zloymalefic/bc250-case/references/printables-1793043-nexgen-pro-v2/AIO Mount/clamping-plate-v2.3mf

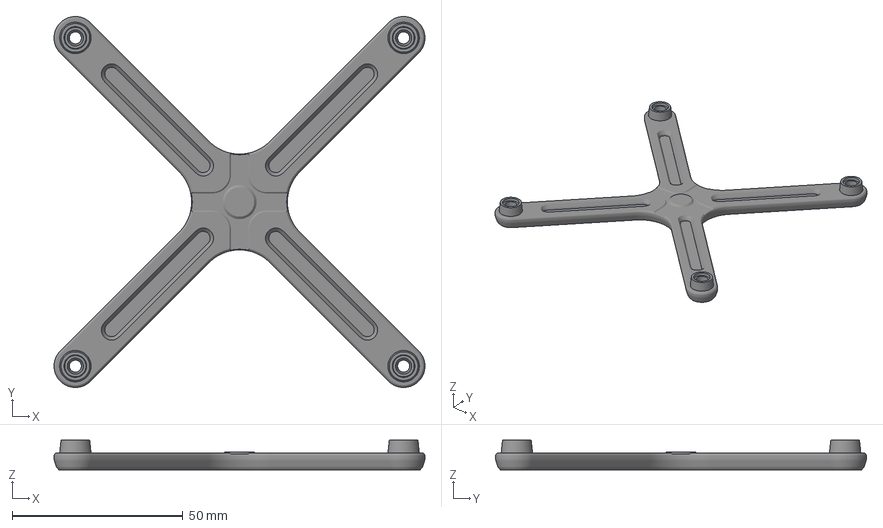
[picture p15: CAD file, 2026-08-19]
references/printables-1793043-nexgen-pro-v2/AIO Mount/clamping-plate-v2.3mf
108.5 x 108.5 x 8.70 mm
