zloymalefic/bc250-case/references/printables-1793043-nexgen-pro-v2/ARGB LED Strip/pro-v2-argb-strip-mount.3mf

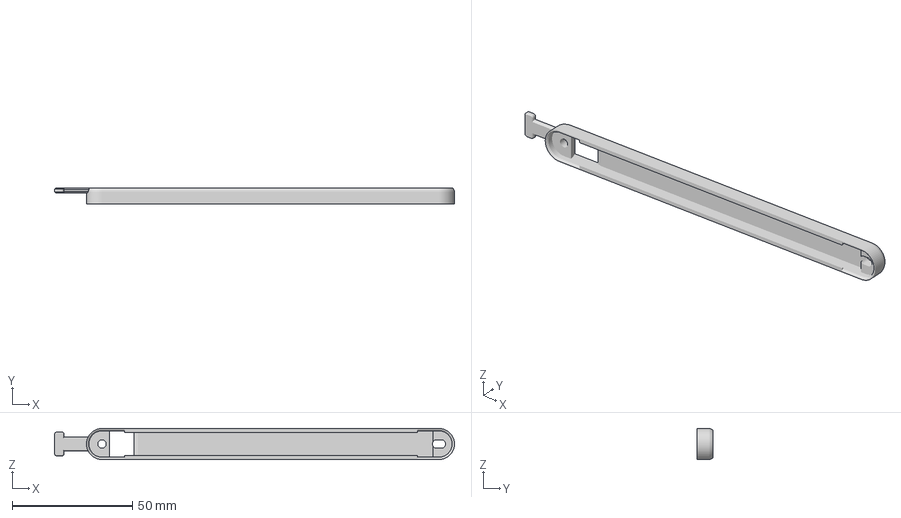
[picture p16: CAD file, 2026-08-19]
references/printables-1793043-nexgen-pro-v2/ARGB LED Strip/pro-v2-argb-strip-mount.3mf
166.2 x 6.60 x 12.9 mm
