zloymalefic/bc250-case/references/printables-1793043-nexgen-pro-v2/Case/pro-v2-rear-case-multi-material.3mf

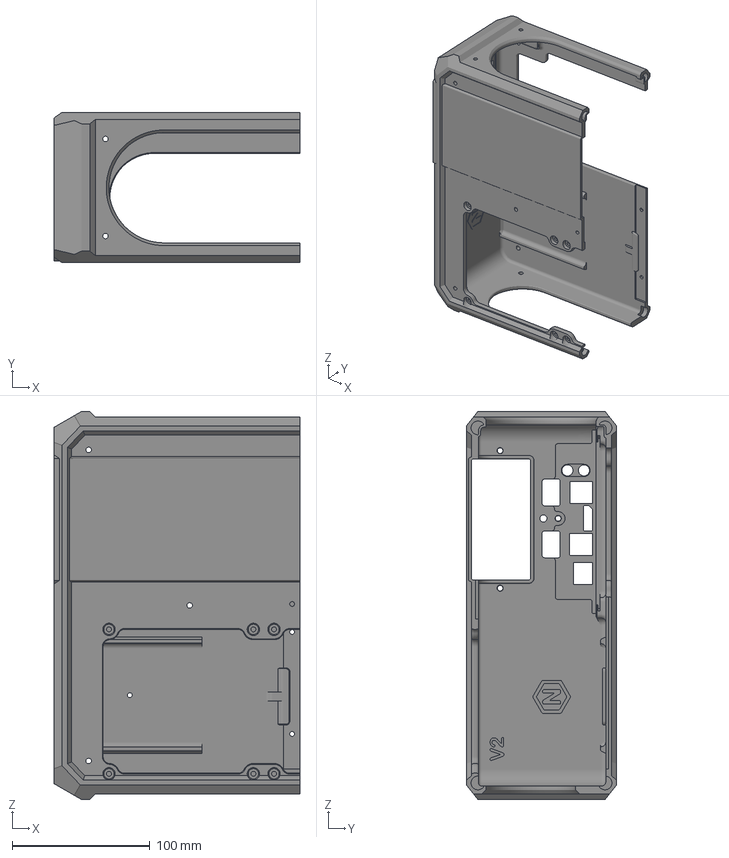
[picture p17: CAD file, 2026-08-19]
references/printables-1793043-nexgen-pro-v2/Case/pro-v2-rear-case-multi-material.3mf
178.6 x 109.4 x 282.1 mm
Case
IO (1)
IO (10)
IO (2)
IO (3)
IO (5)
IO (7)
IO (8)
IO (9)
Lan (1)
Lan (2)
Lan
NXG-Logo-1
NXG-Logo-2
Network Logo
PWR (1)
PWR (2)
PWR
PWR-Loop
RST (1)
RST (2)
RST
RST-Loop
