zloymalefic/bc250-case/references/printables-1793043-nexgen-pro-v2/Foot/pro-long-foot-tpu.3mf

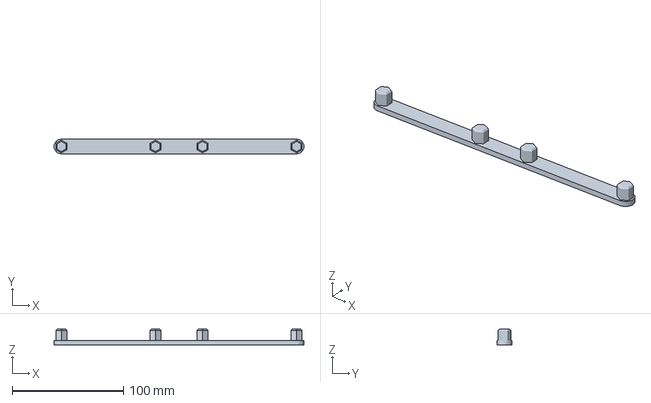
[picture p18: CAD file, 2026-08-19]
references/printables-1793043-nexgen-pro-v2/Foot/pro-long-foot-tpu.3mf
225.2 x 13.2 x 14.0 mm
