zloymalefic/bc250-case/references/printables-1793043-nexgen-pro-v2/Latest Face Plate Design - (Version 2.1)/blank-face-plate.step

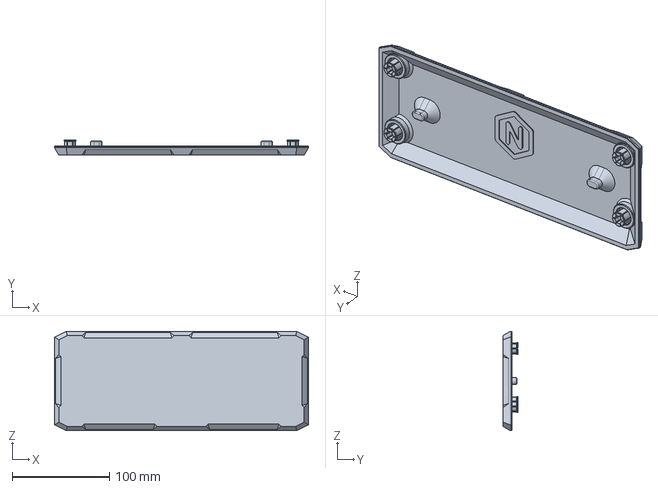
[picture p19: CAD file, 2026-08-19]
references/printables-1793043-nexgen-pro-v2/Latest Face Plate Design - (Version 2.1)/blank-face-plate.step
260.9 x 15.7 x 102.0 mm
