zloymalefic/bc250-case/references/printables-1793043-nexgen-pro-v2/Left Hand Hex Panel/pro-v2-lh-hex-panel-no-logo-edition.3mf

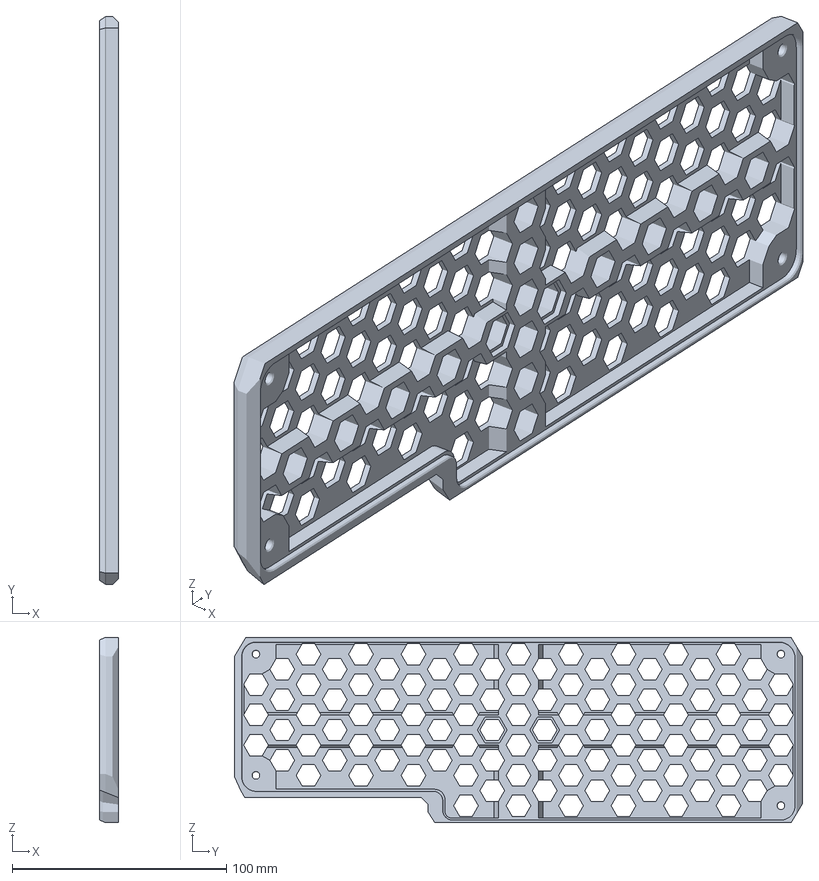
[picture p20: CAD file, 2026-08-19]
references/printables-1793043-nexgen-pro-v2/Left Hand Hex Panel/pro-v2-lh-hex-panel-no-logo-edition.3mf
9.00 x 264.9 x 86.4 mm
