zloymalefic/bc250-case/references/printables-1793043-nexgen-pro-v2/Power Button/pro-v2-button-mounting-plate.3mf

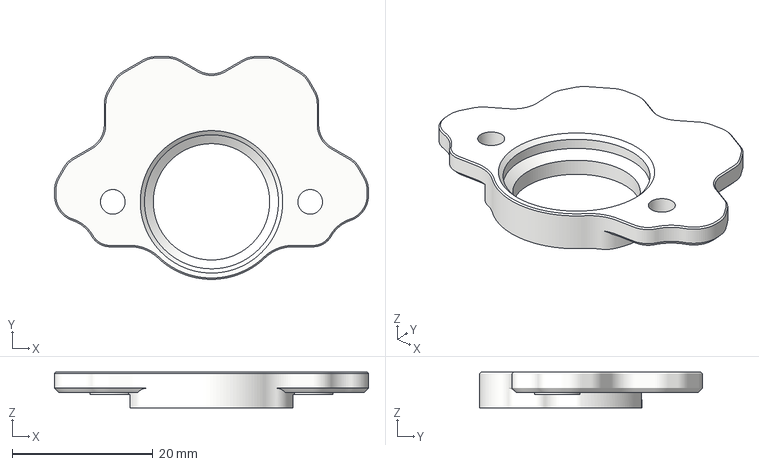
[picture p21: CAD file, 2026-08-19]
references/printables-1793043-nexgen-pro-v2/Power Button/pro-v2-button-mounting-plate.3mf
44.5 x 31.6 x 5.10 mm
