zloymalefic/bc250-case/references/printables-1793043-nexgen-pro-v2/Power Supply Mounts/pro-v2-meanwell-lop-mount-400-500-600.3mf

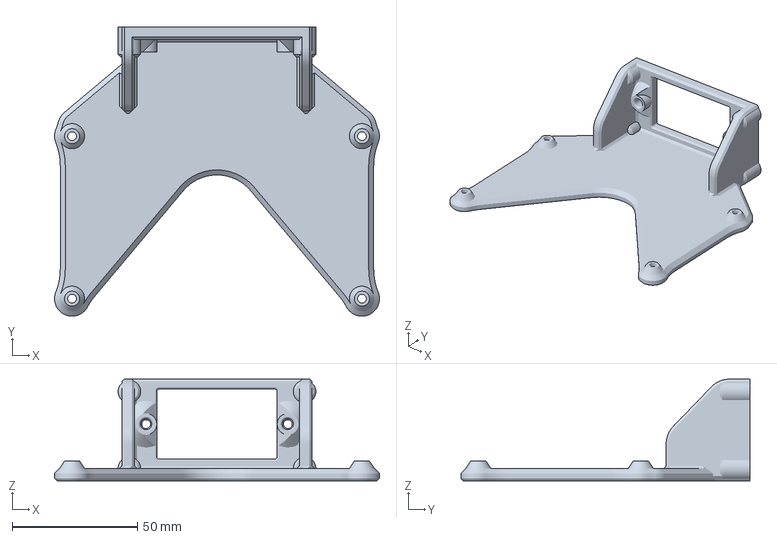
[picture p22: CAD file, 2026-08-19]
references/printables-1793043-nexgen-pro-v2/Power Supply Mounts/pro-v2-meanwell-lop-mount-400-500-600.3mf
129.6 x 115.4 x 40.6 mm
