zloymalefic/bc250-case/references/printables-1793043-nexgen-pro-v2/Right Hand Hex Panel/pro-v2-rh-hex-panel-rune-stone-edition.3mf

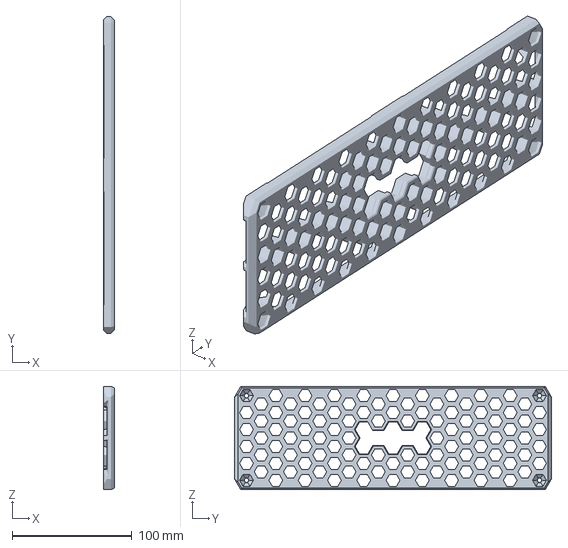
[picture p23: CAD file, 2026-08-19]
references/printables-1793043-nexgen-pro-v2/Right Hand Hex Panel/pro-v2-rh-hex-panel-rune-stone-edition.3mf
9.00 x 264.9 x 86.4 mm
