zloymalefic/bc250-case/references/printables-1793043-nexgen-pro-v2/Top and Bottom Hex Panels/pro-v2-top-hex-panel.3mf

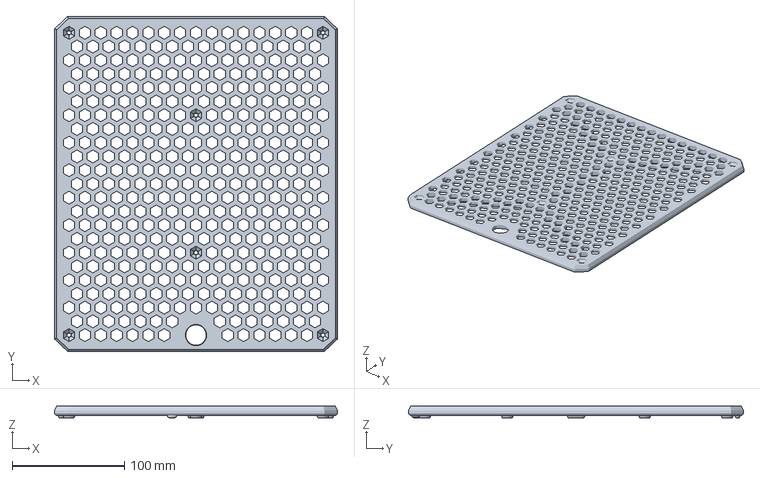
[picture p24: CAD file, 2026-08-19]
references/printables-1793043-nexgen-pro-v2/Top and Bottom Hex Panels/pro-v2-top-hex-panel.3mf
252.1 x 298.5 x 10.9 mm
