zloymalefic/bc250-case/references/printables-1793043-nexgen-pro-v2/Vertical Stand/vertical-stand-optio-1-tpu.3mf

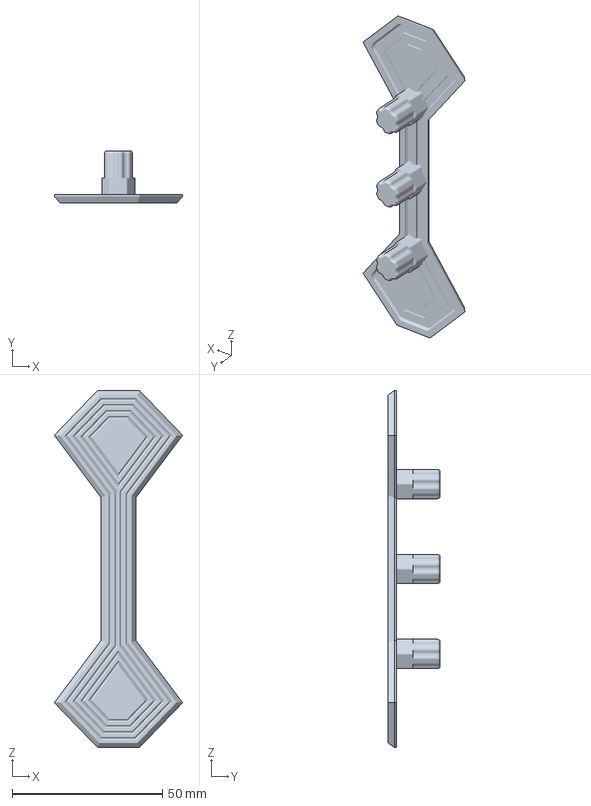
[picture p25: CAD file, 2026-08-19]
references/printables-1793043-nexgen-pro-v2/Vertical Stand/vertical-stand-optio-1-tpu.3mf
42.7 x 17.4 x 118.8 mm
