zloymalefic/bc250-case/visualization/assets/esp32-cover.stl

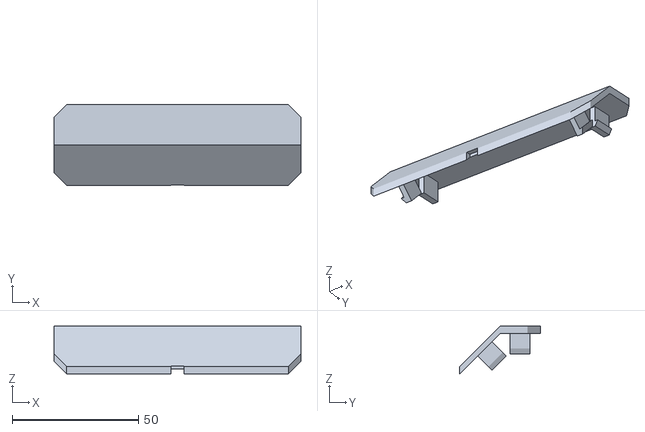
[picture p26: CAD file, 2026-08-20]
visualization/assets/esp32-cover.stl
98.0 x 32.0 x 19.0
