zloymalefic/bc250-case/references/printables-1649679-nexgen-redux/Case V4.2 - Current Version/redux-front-case-42.3mf

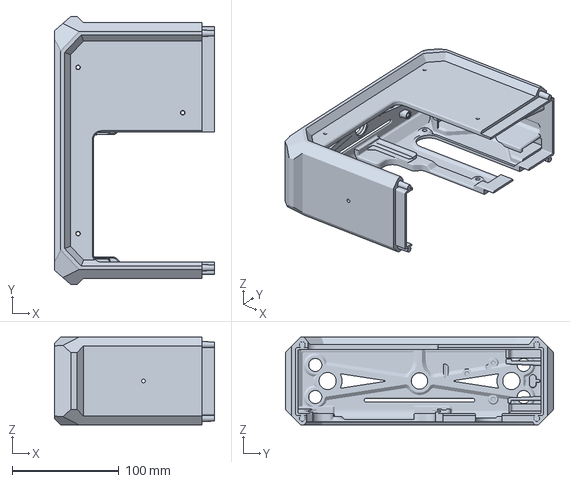
[picture p27: CAD file, 2026-08-20]
references/printables-1649679-nexgen-redux/Case V4.2 - Current Version/redux-front-case-42.3mf
149.7 x 251.1 x 82.3 mm
