zloymalefic/bc250-case/references/printables-1649679-nexgen-redux/Face Plates V4.2/blank-faceplate.step

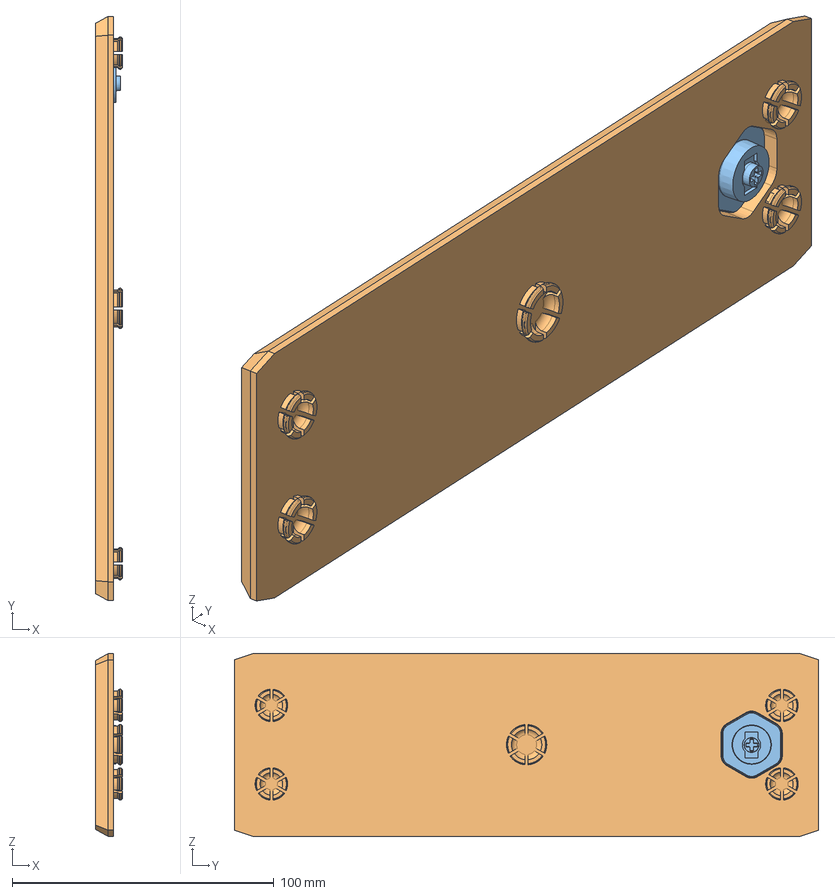
[picture p29: CAD file, 2026-08-20]
references/printables-1649679-nexgen-redux/Face Plates V4.2/blank-faceplate.step
10.2 x 223.2 x 69.9 mm
Blank Button for Generic Latching Switch
Blank REDUX Faceplate
Blank Button for FSP500 PCB
Blank Button to Convert Switch to Momentary
