zloymalefic/bc250-case/references/printables-1649679-nexgen-redux/Fan Mount and Feet V4.2 - Current Version/optional-long-foot-tpu.3mf

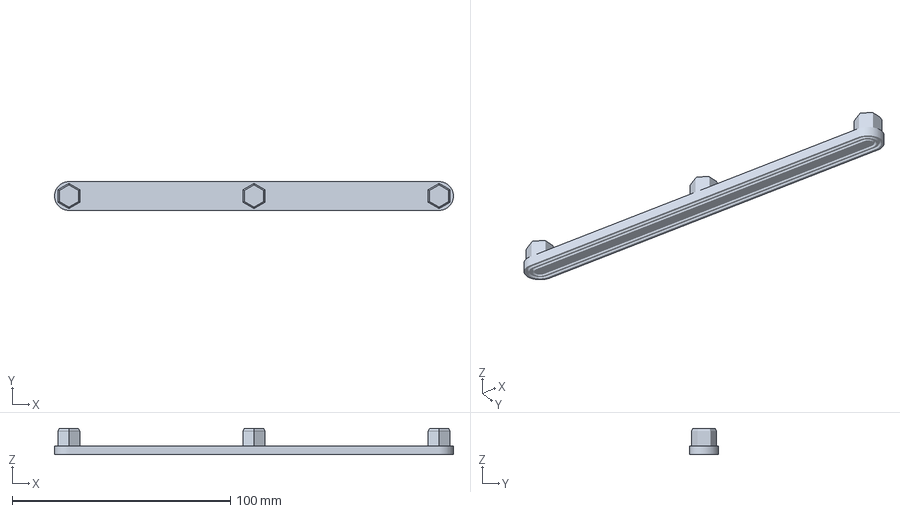
[picture p30: CAD file, 2026-08-20]
references/printables-1649679-nexgen-redux/Fan Mount and Feet V4.2 - Current Version/optional-long-foot-tpu.3mf
182.8 x 13.2 x 12.0 mm
