zloymalefic/bc250-case/references/printables-1649679-nexgen-redux/Optional Parts - Current Version/redux-clamping-plate-v43.3mf

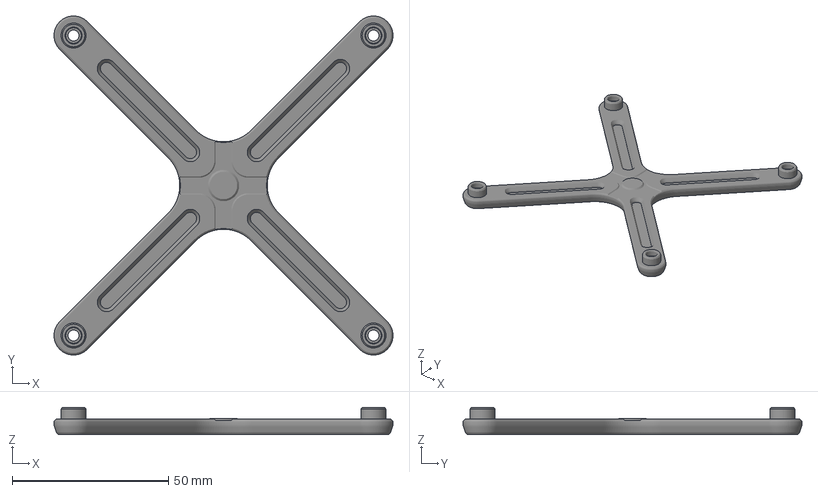
[picture p32: CAD file, 2026-08-20]
references/printables-1649679-nexgen-redux/Optional Parts - Current Version/redux-clamping-plate-v43.3mf
108.5 x 108.5 x 8.80 mm
