zloymalefic/bc250-case/references/printables-1649679-nexgen-redux/Split Hex Covers for 220x220mm or Larger/top-split-panel-a.3mf

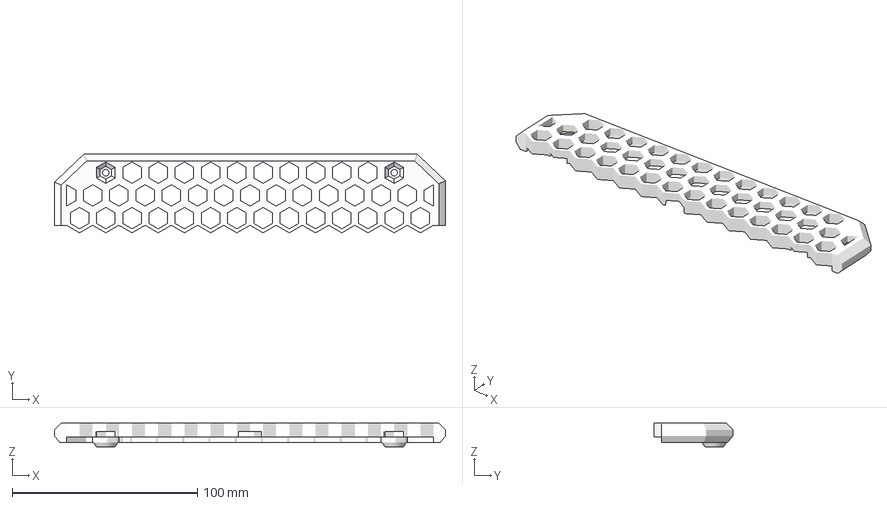
[picture p33: CAD file, 2026-08-20]
references/printables-1649679-nexgen-redux/Split Hex Covers for 220x220mm or Larger/top-split-panel-a.3mf
210.8 x 42.4 x 12.9 mm
