zloymalefic/bc250-case/references/printables-1649679-nexgen-redux/Split Hex Covers for Odd Ball Prusa Beds (250x210)/prusa-priners-only-joiner.3mf

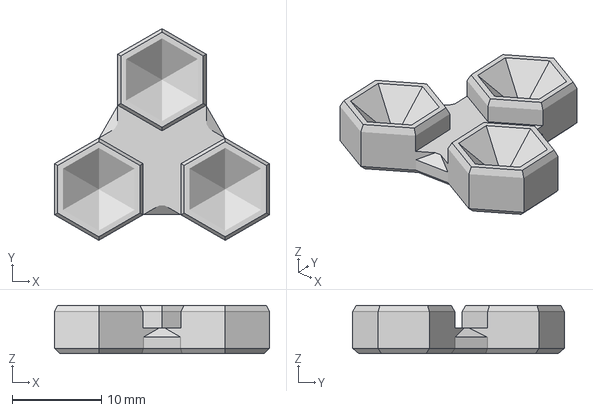
[picture p34: CAD file, 2026-08-20]
references/printables-1649679-nexgen-redux/Split Hex Covers for Odd Ball Prusa Beds (250x210)/prusa-priners-only-joiner.3mf
24.0 x 23.7 x 5.40 mm
