zloymalefic/bc250-case/references/printables-1652979-quiet-case/Deepcool Edition - Digital Display/back-case.stl

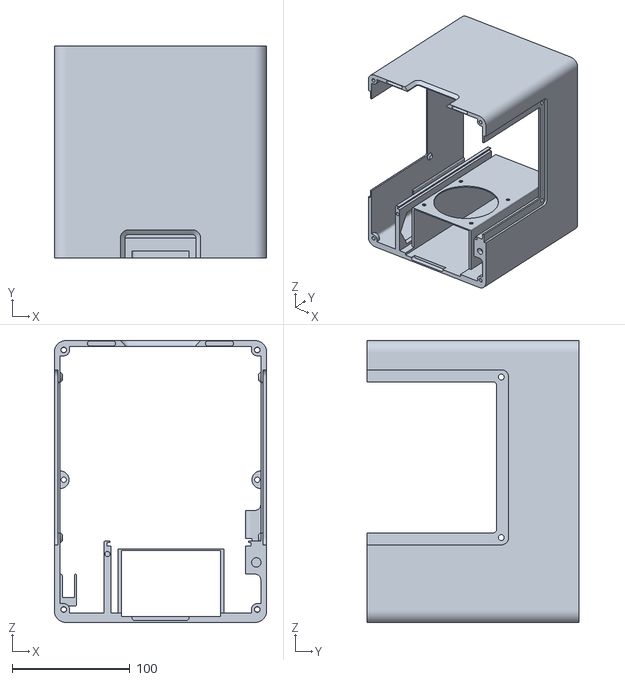
[picture p35: CAD file, 2026-08-19]
references/printables-1652979-quiet-case/Deepcool Edition - Digital Display/back-case.stl
180.0 x 180.0 x 239.0
