zloymalefic/bc250-case/references/printables-1652979-quiet-case/XL Version - Aftermath/panel-front.stl

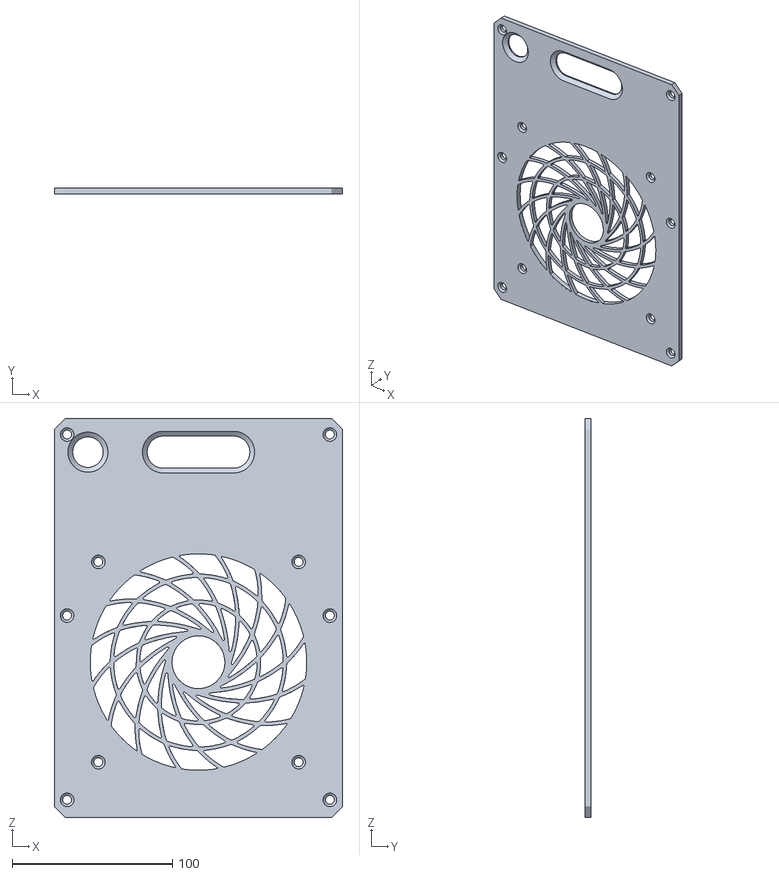
[picture p36: CAD file, 2026-08-19]
references/printables-1652979-quiet-case/XL Version - Aftermath/panel-front.stl
180.0 x 4.01 x 249.0
