zloymalefic/bc250-case/references/printables-1793043-nexgen-pro-v2/AIO Mount/thermalright-mount-bottom-v2.3mf

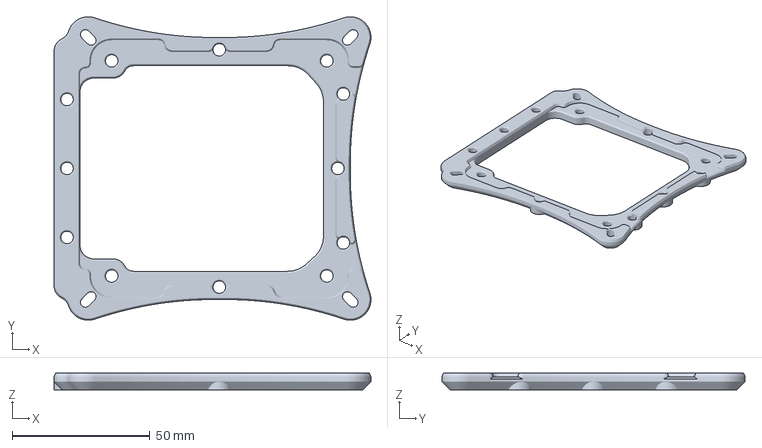
[picture p38: CAD file, 2026-08-19]
references/printables-1793043-nexgen-pro-v2/AIO Mount/thermalright-mount-bottom-v2.3mf
114.9 x 110.0 x 6.10 mm
