zloymalefic/bc250-case/references/printables-1793043-nexgen-pro-v2/ARGB LED Strip/pro-v2-diffuser.3mf

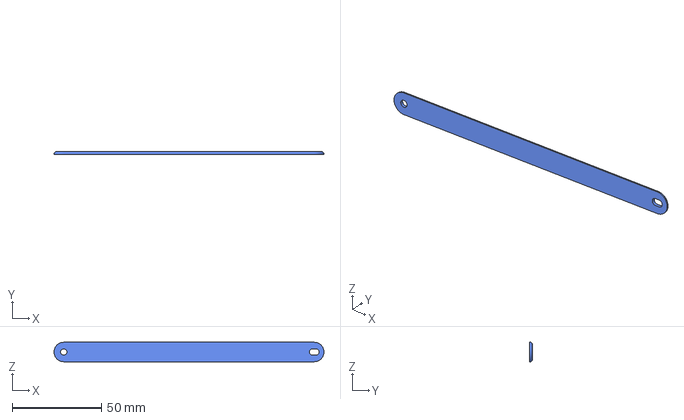
[picture p39: CAD file, 2026-08-19]
references/printables-1793043-nexgen-pro-v2/ARGB LED Strip/pro-v2-diffuser.3mf
150.9 x 1.40 x 10.9 mm
