zloymalefic/bc250-case/references/printables-1793043-nexgen-pro-v2/Case/pro-v2-front-case.3mf

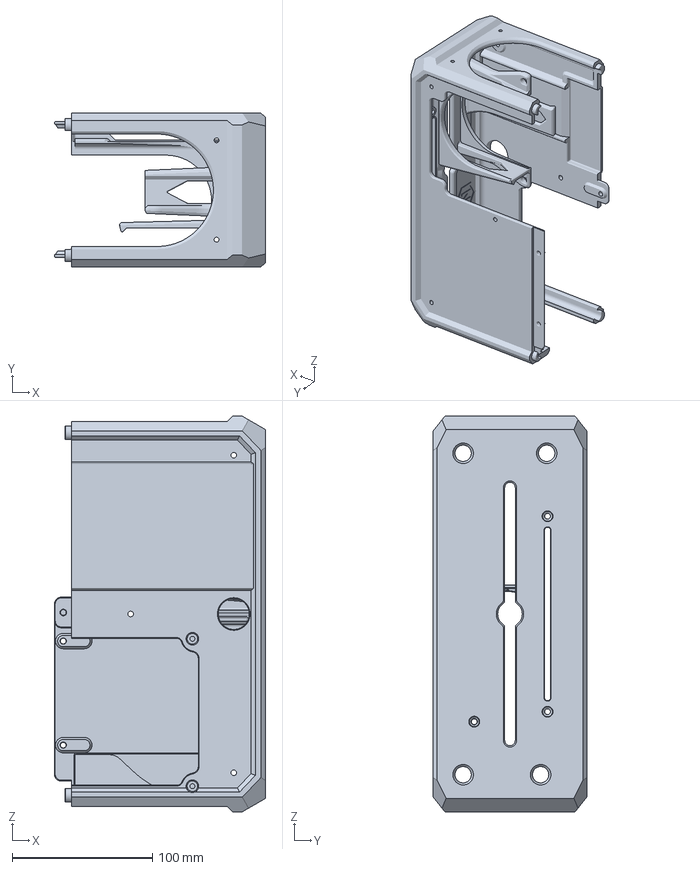
[picture p40: CAD file, 2026-08-19]
references/printables-1793043-nexgen-pro-v2/Case/pro-v2-front-case.3mf
150.5 x 109.4 x 282.0 mm
