zloymalefic/bc250-case/references/printables-1793043-nexgen-pro-v2/Foot/pro-long-foot-petg.3mf

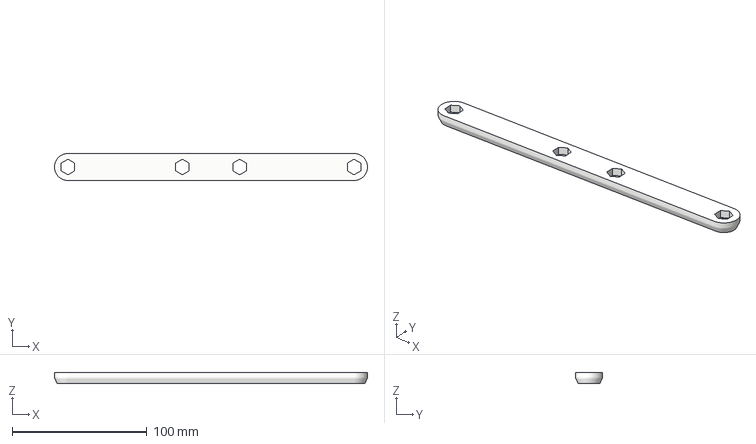
[picture p41: CAD file, 2026-08-19]
references/printables-1793043-nexgen-pro-v2/Foot/pro-long-foot-petg.3mf
232.0 x 20.0 x 8.00 mm
