zloymalefic/bc250-case/references/printables-1793043-nexgen-pro-v2/Latest Face Plate Design - (Version 2.1)/faceplate-option-1.3mf

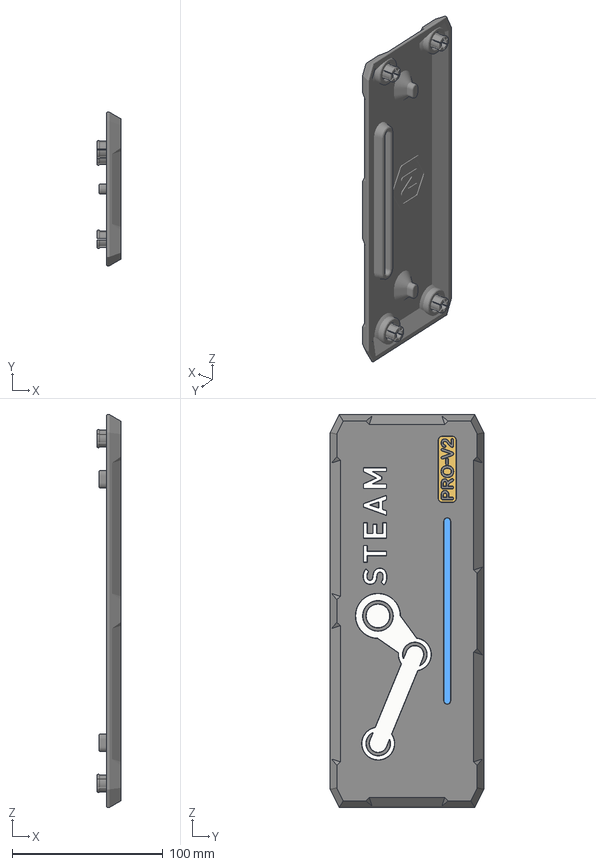
[picture p42: CAD file, 2026-08-19]
references/printables-1793043-nexgen-pro-v2/Latest Face Plate Design - (Version 2.1)/faceplate-option-1.3mf
15.7 x 102.0 x 260.9 mm
Faceplate
LED Strip
Pro Label (1)
Pro Label (2)
Pro Label (3)
Pro Label
Steam Logo (1)
Steam Logo (2)
Steam Logo (3)
Steam Logo (4)
Steam Logo (5)
Steam Logo (6)
Steam Logo
