zloymalefic/bc250-case/references/printables-1793043-nexgen-pro-v2/Left Hand Hex Panel/pro-v2-lh-hex-panel-logo-edition.3mf

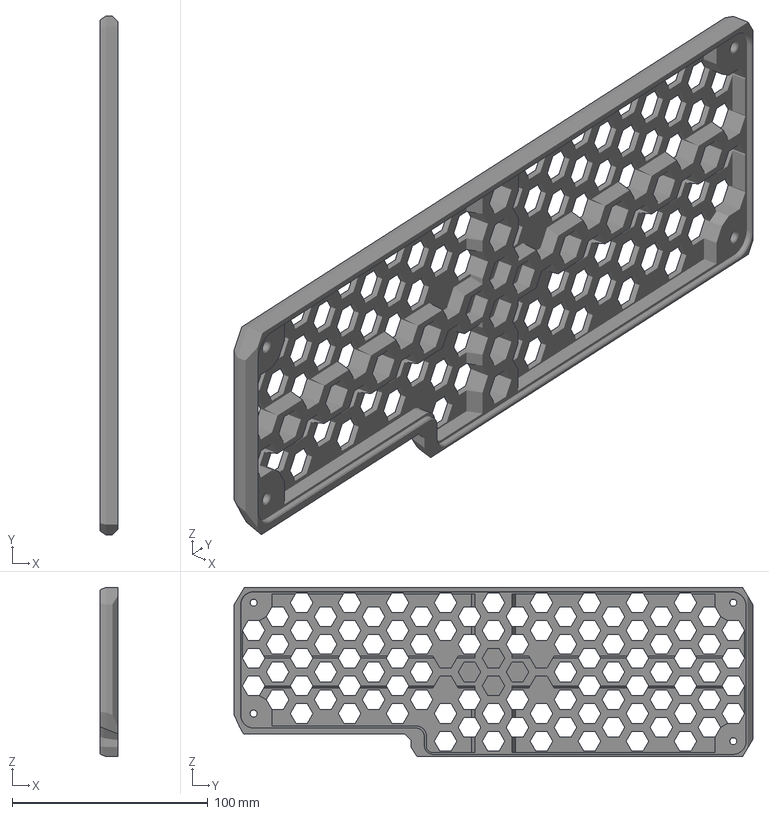
[picture p43: CAD file, 2026-08-19]
references/printables-1793043-nexgen-pro-v2/Left Hand Hex Panel/pro-v2-lh-hex-panel-logo-edition.3mf
9.00 x 264.9 x 86.4 mm
BC-250-Logo (1)
BC-250-Logo (2)
BC-250-Logo (3)
BC-250-Logo
LH Hex Panel (1)
