zloymalefic/bc250-case/references/printables-1793043-nexgen-pro-v2/Power Button/pro-v2-transparent-rear-section.3mf

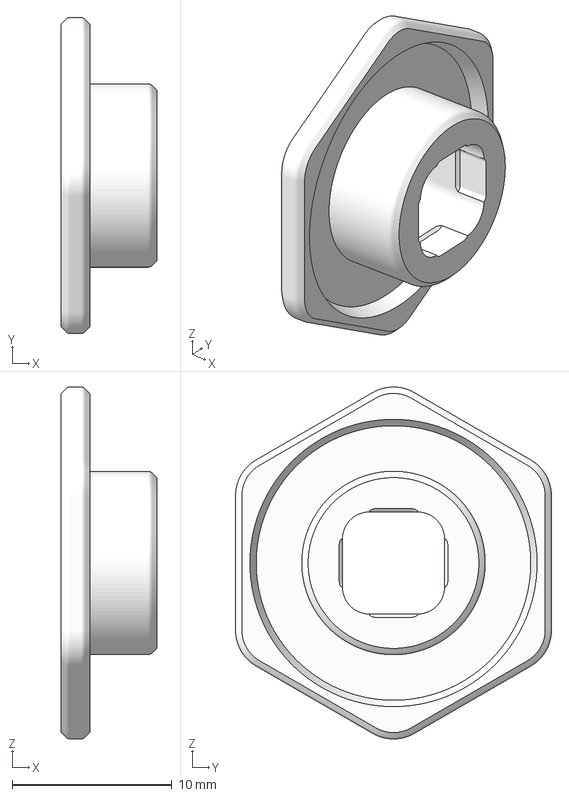
[picture p44: CAD file, 2026-08-19]
references/printables-1793043-nexgen-pro-v2/Power Button/pro-v2-transparent-rear-section.3mf
6.00 x 19.8 x 22.1 mm
