zloymalefic/bc250-case/references/printables-1793043-nexgen-pro-v2/Power Supply Mounts/pro-v2-meanwell-lop-backplate-400-500-600.3mf

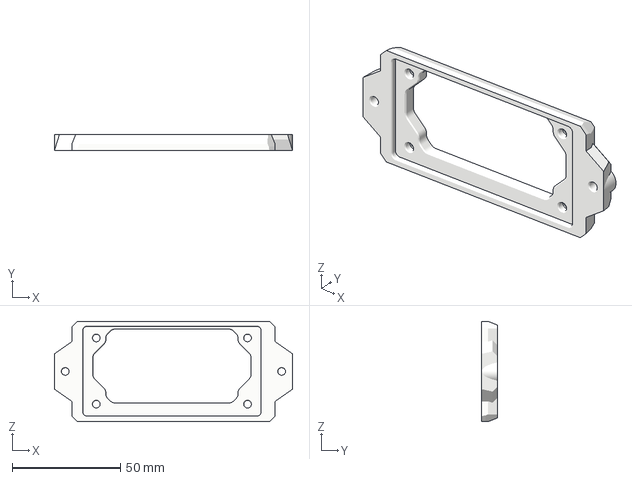
[picture p45: CAD file, 2026-08-19]
references/printables-1793043-nexgen-pro-v2/Power Supply Mounts/pro-v2-meanwell-lop-backplate-400-500-600.3mf
110.0 x 7.20 x 46.3 mm
