zloymalefic/bc250-case/references/printables-1793043-nexgen-pro-v2/Right Hand Hex Panel/rune-stone-argb.3mf

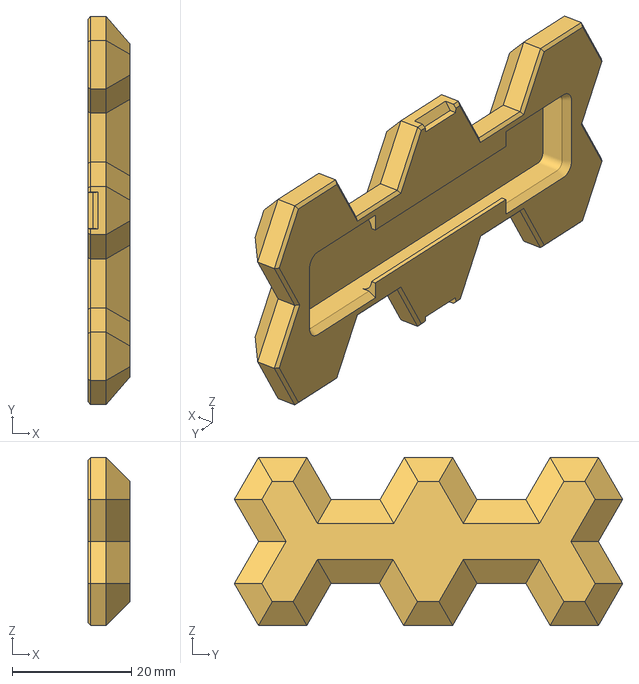
[picture p46: CAD file, 2026-08-19]
references/printables-1793043-nexgen-pro-v2/Right Hand Hex Panel/rune-stone-argb.3mf
7.00 x 65.2 x 28.2 mm
