zloymalefic/bc250-case/references/printables-1793043-nexgen-pro-v2/Vertical Stand/vertical-stand-optio-1-petg.3mf

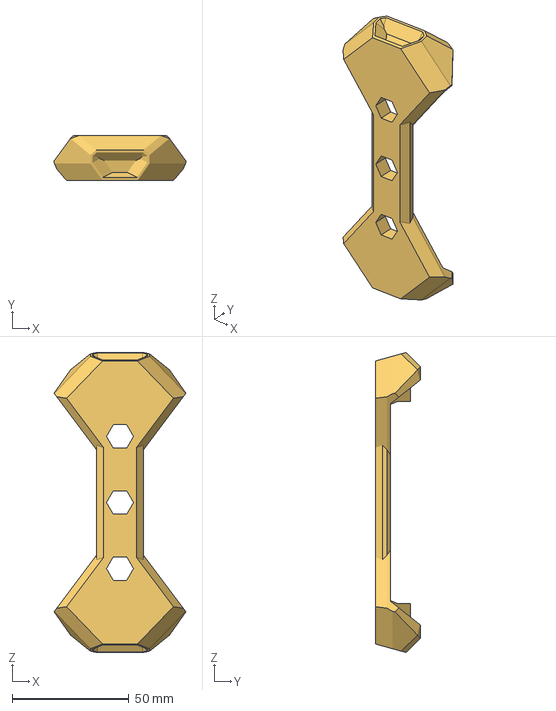
[picture p47: CAD file, 2026-08-19]
references/printables-1793043-nexgen-pro-v2/Vertical Stand/vertical-stand-optio-1-petg.3mf
56.5 x 19.4 x 128.4 mm
