zloymalefic/bc250-case/visualization/assets/rear-core.stl

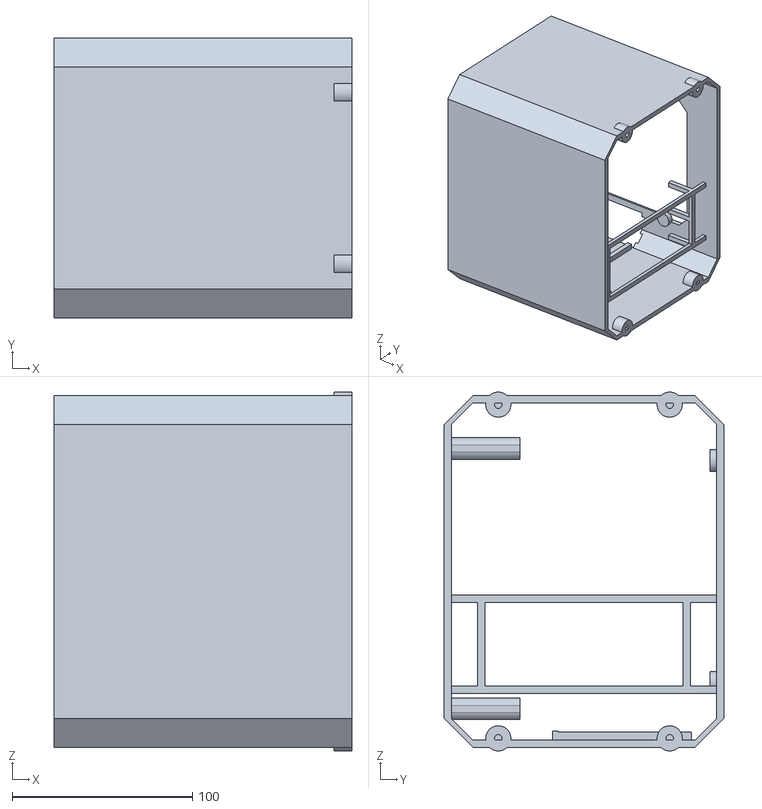
[picture p48: CAD file, 2026-08-20]
visualization/assets/rear-core.stl
165.0 x 155.0 x 199.0
