zloymalefic/bc250-case/references/printables-1649679-nexgen-redux/Case V4.2 - Current Version/redux-optional-usb-cover.3mf

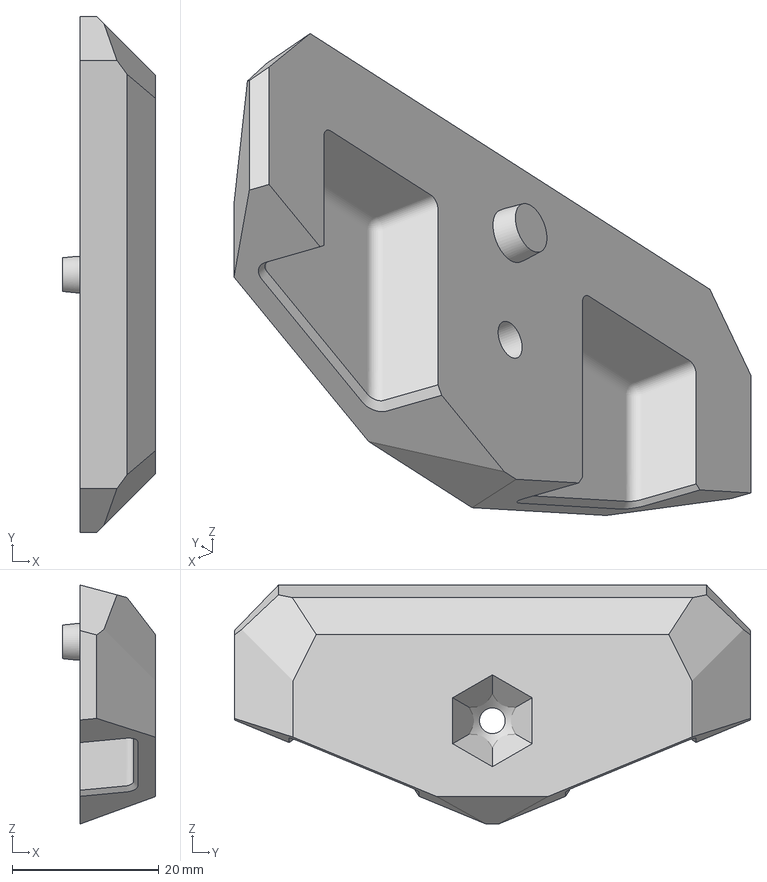
[picture p49: CAD file, 2026-08-20]
references/printables-1649679-nexgen-redux/Case V4.2 - Current Version/redux-optional-usb-cover.3mf
12.7 x 70.4 x 32.6 mm
