zloymalefic/bc250-case/references/printables-1649679-nexgen-redux/Face Plates V4.2.1 - Current Version/steam-faceplate.3mf

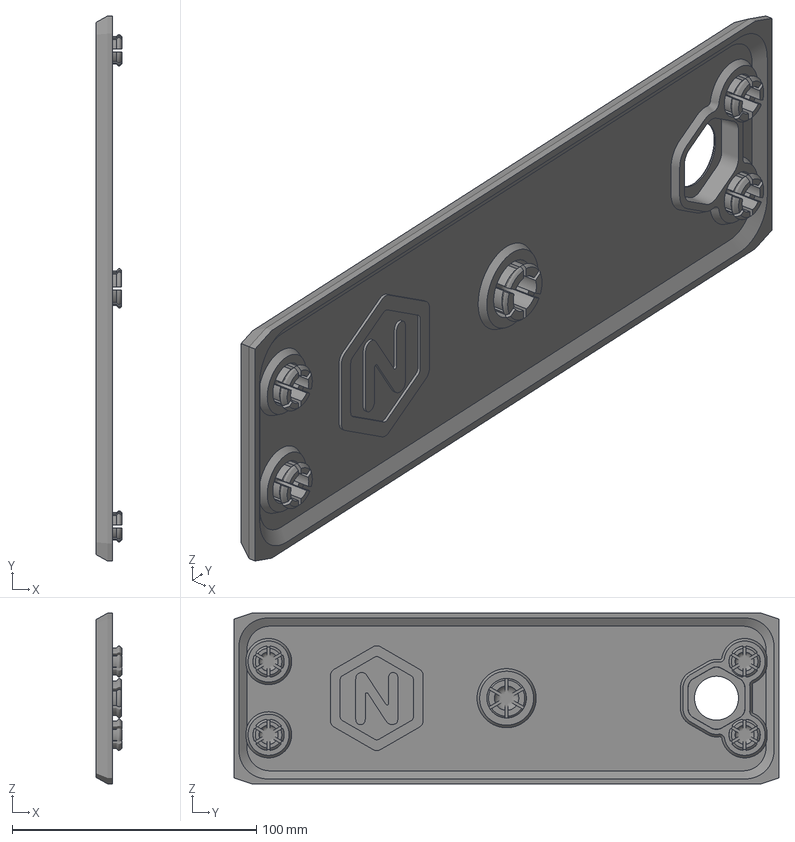
[picture p50: CAD file, 2026-08-20]
references/printables-1649679-nexgen-redux/Face Plates V4.2.1 - Current Version/steam-faceplate.3mf
10.8 x 223.2 x 69.9 mm
REDUX - Blank Faceplate v4.2 (1)
Redux-1
Redux-2
Redux-3
Steam (1)
Steam (2)
Steam (3)
Steam (4)
Steam (5)
Steam (6)
Steam
