zloymalefic/bc250-case/references/printables-1649679-nexgen-redux/Fan Mount and Feet V4.2 - Current Version/redux-fan-mount.3mf

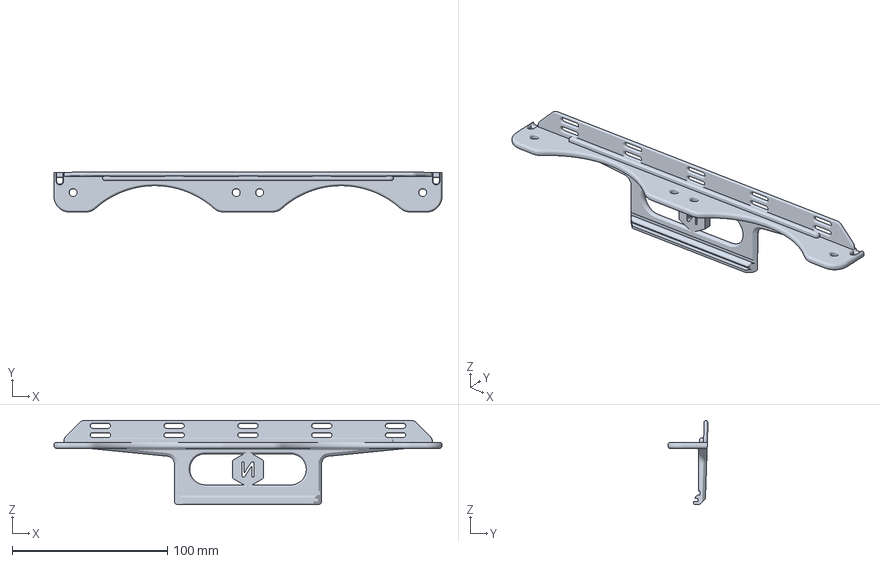
[picture p52: CAD file, 2026-08-20]
references/printables-1649679-nexgen-redux/Fan Mount and Feet V4.2 - Current Version/redux-fan-mount.3mf
249.7 x 25.9 x 54.1 mm
