zloymalefic/bc250-case/references/printables-1649679-nexgen-redux/Hex Covers for 300x300 Beds - Current Version/redux-bottom-hex-cover.3mf

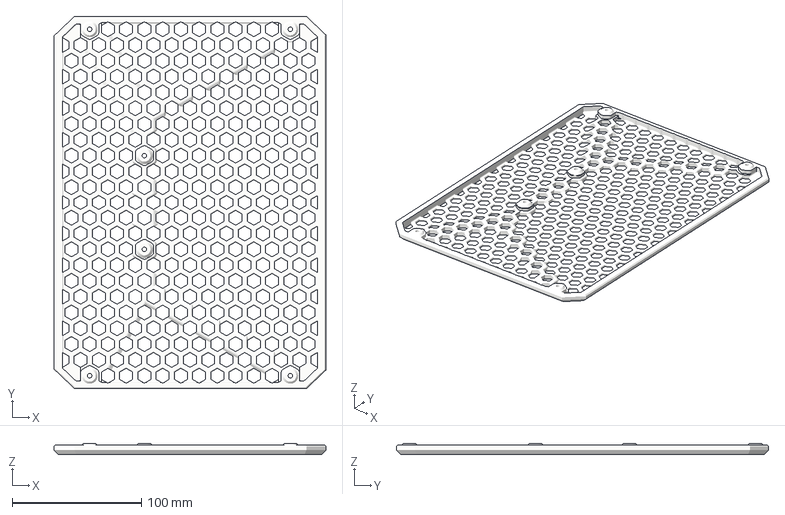
[picture p53: CAD file, 2026-08-20]
references/printables-1649679-nexgen-redux/Hex Covers for 300x300 Beds - Current Version/redux-bottom-hex-cover.3mf
210.8 x 288.5 x 8.90 mm
