zloymalefic/bc250-case/references/printables-1649679-nexgen-redux/Optional Parts - Current Version/redux-vertical-stand-optional.3mf

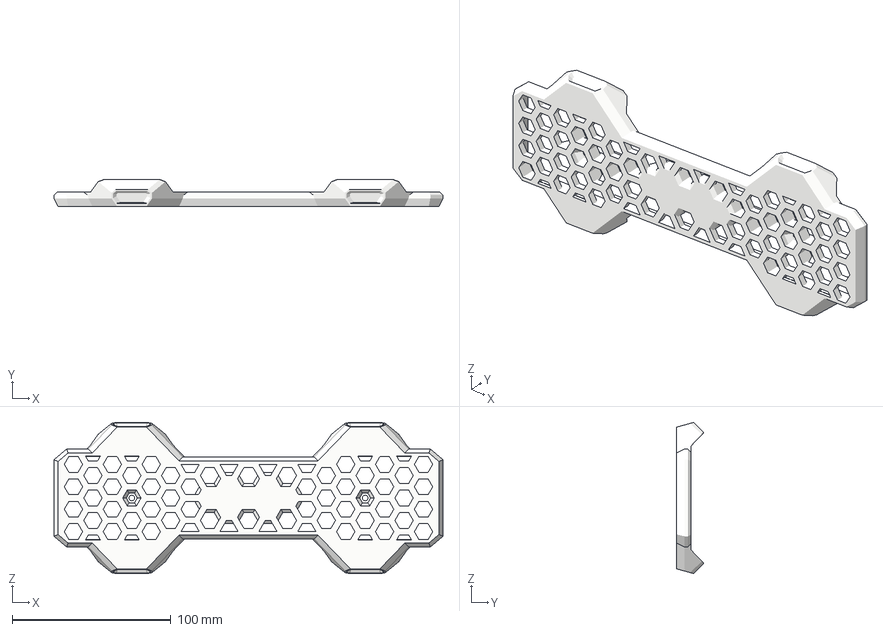
[picture p54: CAD file, 2026-08-20]
references/printables-1649679-nexgen-redux/Optional Parts - Current Version/redux-vertical-stand-optional.3mf
244.9 x 16.8 x 95.1 mm
