zloymalefic/bc250-case/references/printables-1652979-quiet-case/Deepcool Edition - Digital Display/stand.stl

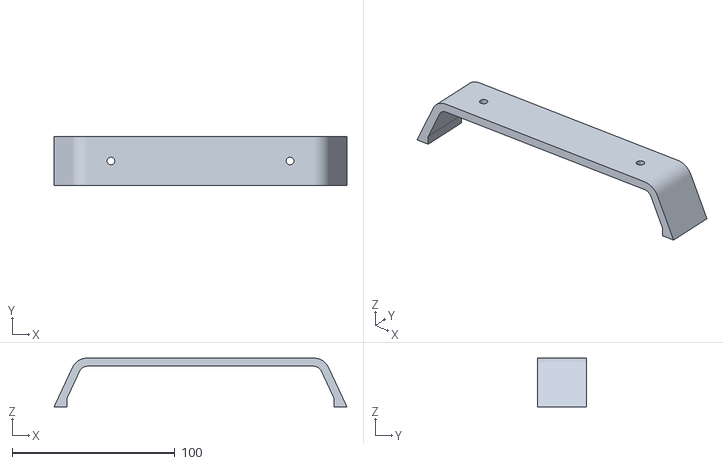
[picture p56: CAD file, 2026-08-19]
references/printables-1652979-quiet-case/Deepcool Edition - Digital Display/stand.stl
180.0 x 30.0 x 30.0
