zloymalefic/bc250-case/references/printables-1652979-quiet-case/XL Version - Aftermath/panel-back.stl

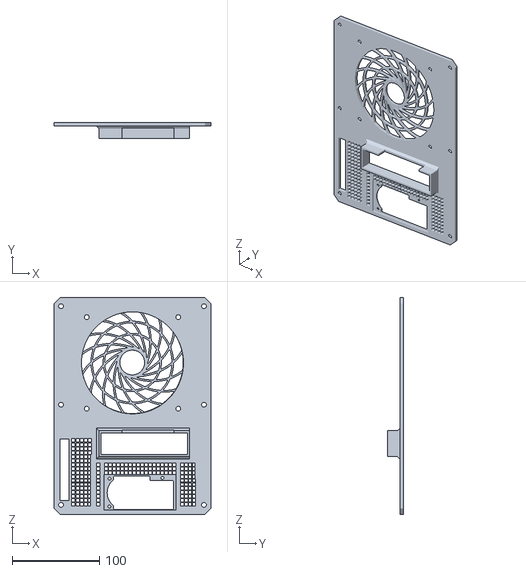
[picture p57: CAD file, 2026-08-19]
references/printables-1652979-quiet-case/XL Version - Aftermath/panel-back.stl
180.0 x 18.5 x 249.0
