zloymalefic/bc250-case/references/printables-1737913-nyacom-flex/body-cover-magnetic-rail-b-v2.stl

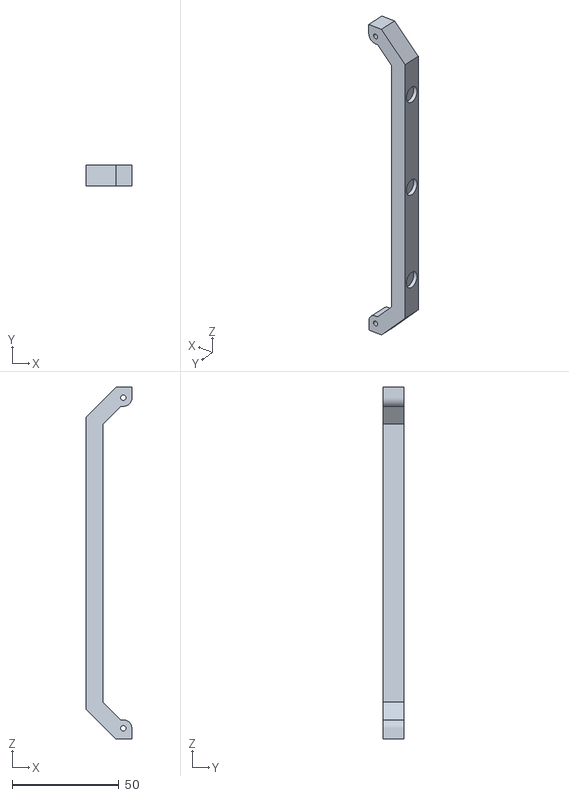
[picture p58: CAD file, 2026-08-19]
references/printables-1737913-nyacom-flex/body-cover-magnetic-rail-b-v2.stl
21.6 x 10.0 x 165.0
