zloymalefic/bc250-case/references/printables-1793043-nexgen-pro-v2/Case/pro-v2-usb-cover-multi-material.3mf

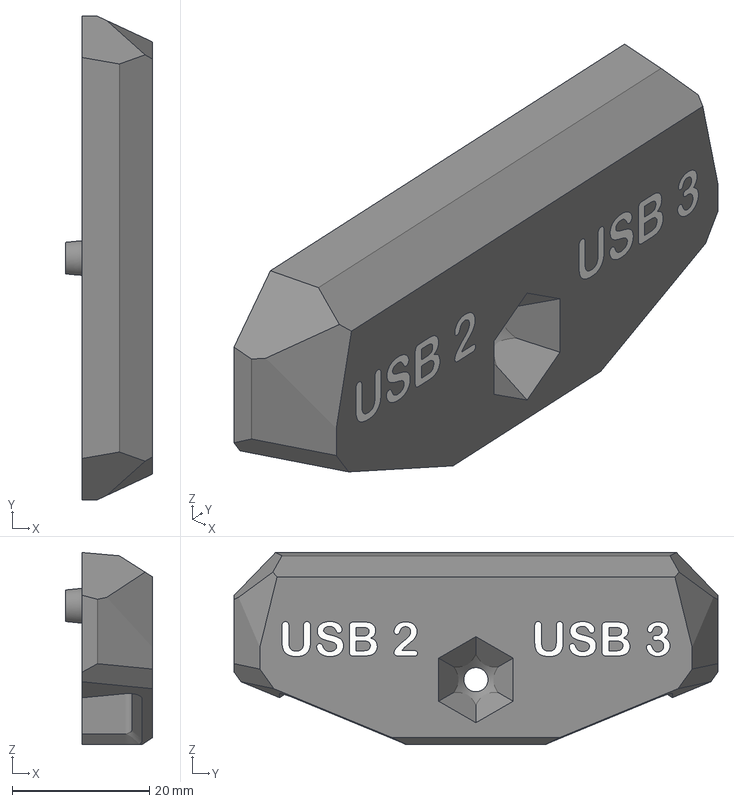
[picture p60: CAD file, 2026-08-19]
references/printables-1793043-nexgen-pro-v2/Case/pro-v2-usb-cover-multi-material.3mf
12.6 x 70.4 x 27.9 mm
Cover
Text (1)
Text (2)
Text (3)
Text (4)
Text (5)
Text (6)
Text (7)
Text
