zloymalefic/bc250-case/references/printables-1793043-nexgen-pro-v2/Latest Face Plate Design - (Version 2.1)/faceplate-option-4.3mf

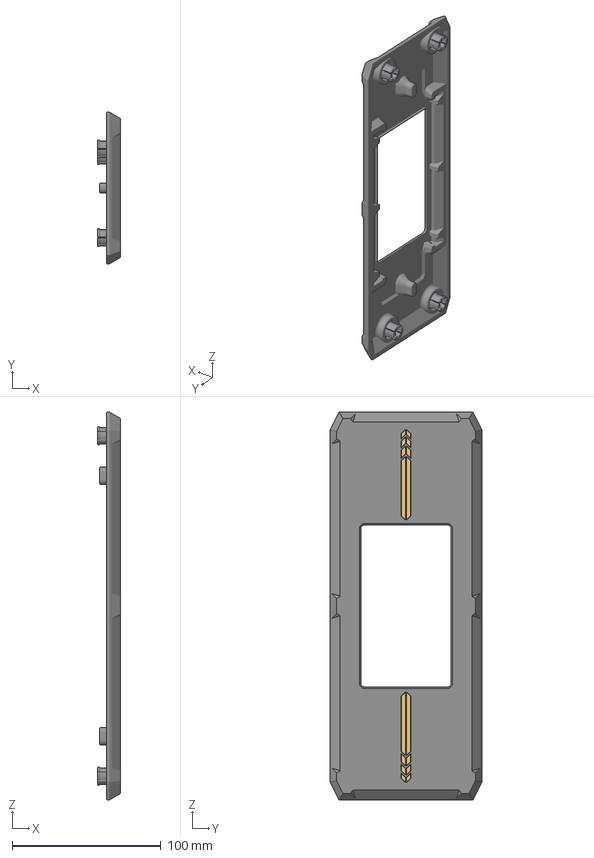
[picture p61: CAD file, 2026-08-19]
references/printables-1793043-nexgen-pro-v2/Latest Face Plate Design - (Version 2.1)/faceplate-option-4.3mf
15.7 x 102.0 x 260.9 mm
Accent (1)
Accent (10)
Accent (11)
Accent (12)
Accent (13)
Accent (14)
Accent (15)
Accent (2)
Accent (3)
Accent (4)
Accent (5)
Accent (6)
Accent (7)
Accent (8)
Accent (9)
Accent
Faceplate-Steam
