zloymalefic/bc250-case/references/printables-1793043-nexgen-pro-v2/Power Supply Mounts/pro-v2-flex-mount-fsp500-and-flex-atx.3mf

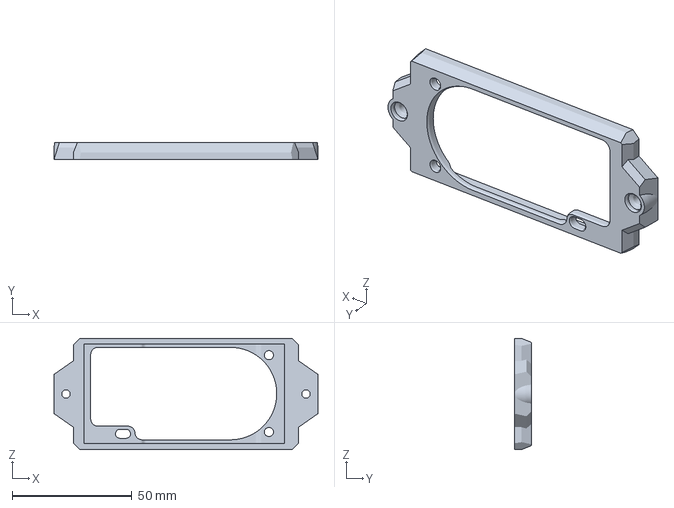
[picture p62: CAD file, 2026-08-19]
references/printables-1793043-nexgen-pro-v2/Power Supply Mounts/pro-v2-flex-mount-fsp500-and-flex-atx.3mf
110.0 x 7.20 x 46.3 mm
