zloymalefic/bc250-case/references/printables-1793043-nexgen-pro-v2/Vertical Stand/vertical-foot-option-2.3mf

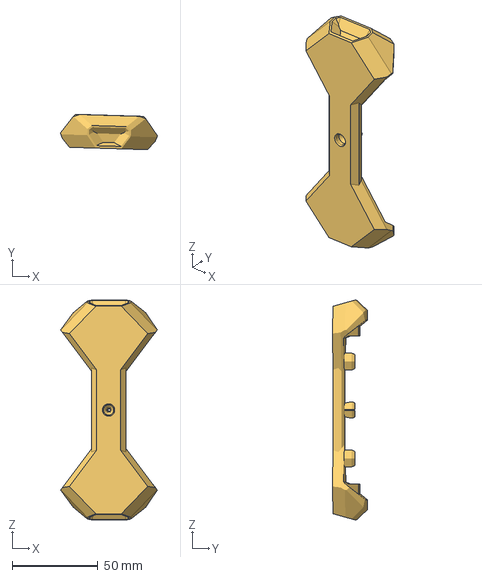
[picture p64: CAD file, 2026-08-19]
references/printables-1793043-nexgen-pro-v2/Vertical Stand/vertical-foot-option-2.3mf
56.4 x 20.6 x 128.4 mm
