zloymalefic/bc250-case/visualization/assets/intake-cover-right.stl

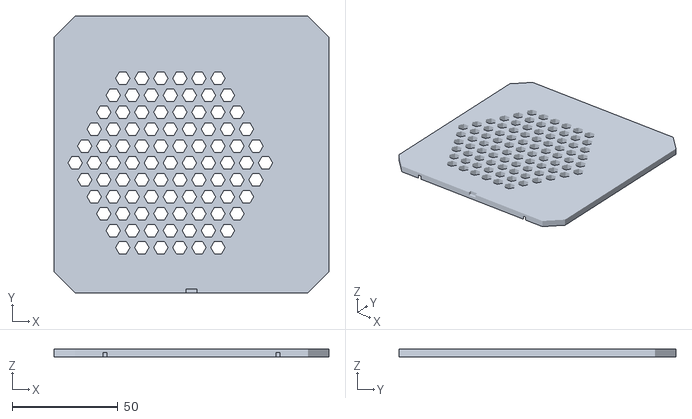
[picture p65: CAD file, 2026-08-20]
visualization/assets/intake-cover-right.stl
130.0 x 131.0 x 4.00
