zloymalefic/bc250-case/cad/exports/fit-calibration-coupon-v0.1.stl

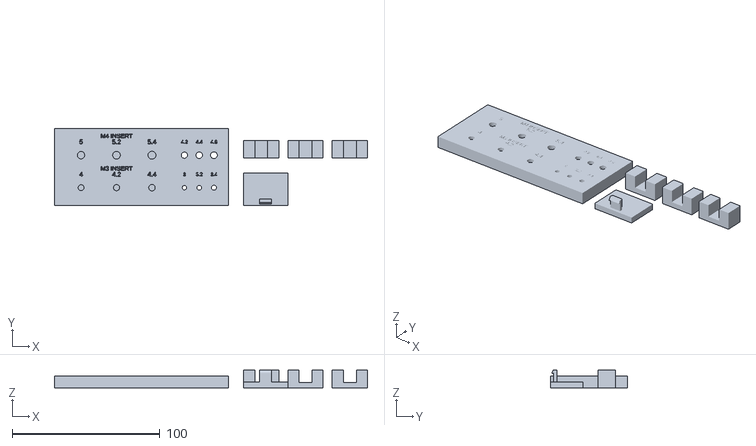
[picture p66: CAD file, 2026-08-20]
cad/exports/fit-calibration-coupon-v0.1.stl
212.0 x 52.0 x 12.0
