zloymalefic/bc250-case/references/printables-1649679-nexgen-redux/Case V4.2 - Current Version/redux-rear-case-mm-non-sata-drive-bay-v42.3mf

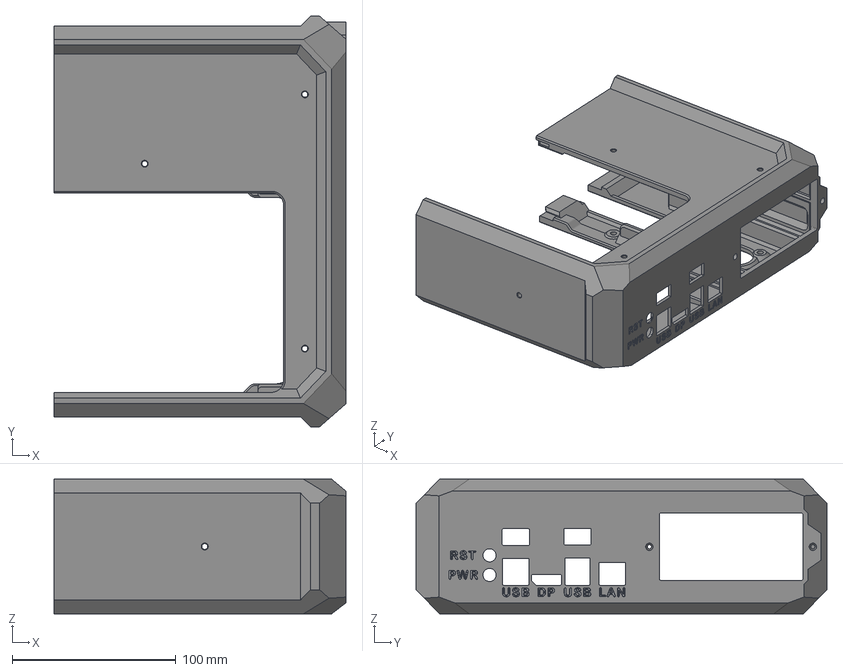
[picture p67: CAD file, 2026-08-20]
references/printables-1649679-nexgen-redux/Case V4.2 - Current Version/redux-rear-case-mm-non-sata-drive-bay-v42.3mf
178.6 x 251.1 x 82.3 mm
REDUX - Rear Case - v4.2
