zloymalefic/bc250-case/references/printables-1649679-nexgen-redux/Face Plates V4.2/simple-accent-button-for-generic-momentary-switch.3mf

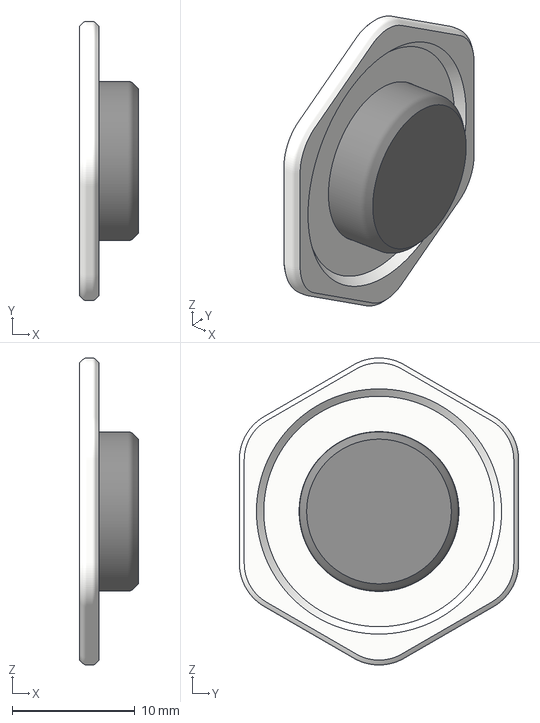
[picture p69: CAD file, 2026-08-20]
references/printables-1649679-nexgen-redux/Face Plates V4.2/simple-accent-button-for-generic-momentary-switch.3mf
4.80 x 22.8 x 25.1 mm
Accent
Button
