zloymalefic/bc250-case/references/printables-1649679-nexgen-redux/Hex Covers for 300x300 Beds - Current Version/redux-rh-side-cover-multi-material.3mf

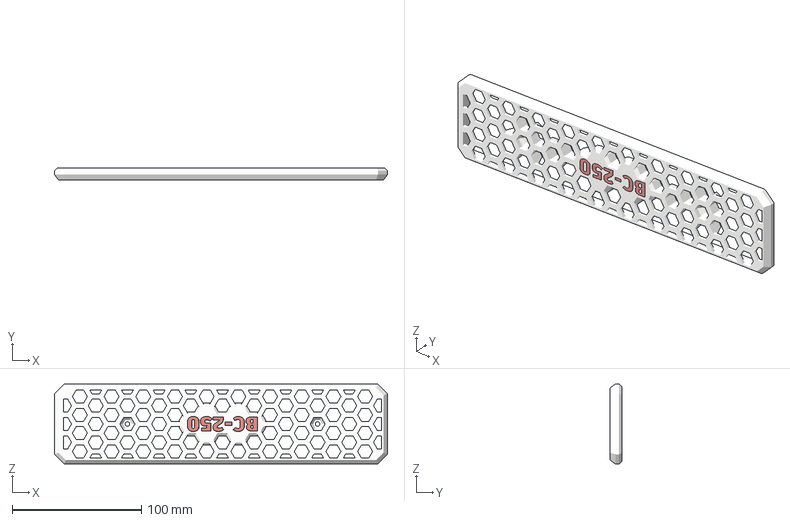
[picture p70: CAD file, 2026-08-20]
references/printables-1649679-nexgen-redux/Hex Covers for 300x300 Beds - Current Version/redux-rh-side-cover-multi-material.3mf
257.2 x 9.00 x 61.8 mm
B
C
Hypen
LH-RH Cover - Hex
