zloymalefic/bc250-case/references/printables-1649679-nexgen-redux/Split Hex Covers for Odd Ball Prusa Beds (250x210)/prusa-priners-only-top-split-panel-a.3mf

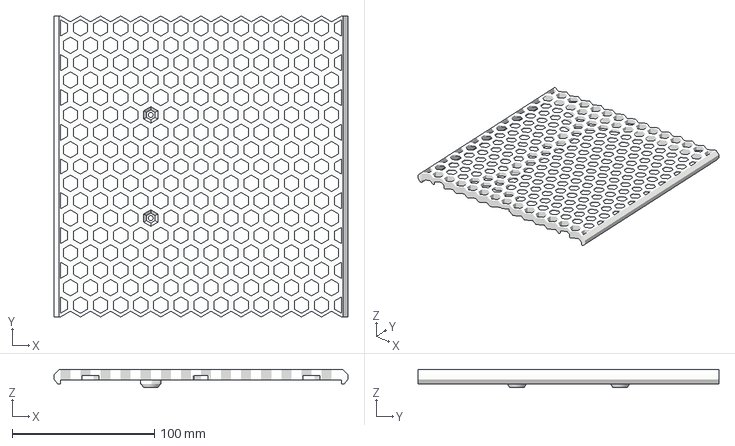
[picture p71: CAD file, 2026-08-20]
references/printables-1649679-nexgen-redux/Split Hex Covers for Odd Ball Prusa Beds (250x210)/prusa-priners-only-top-split-panel-a.3mf
206.8 x 211.8 x 12.9 mm
