zloymalefic/bc250-case/references/printables-1652979-quiet-case/Deepcool Edition - Digital Display/front-case.stl

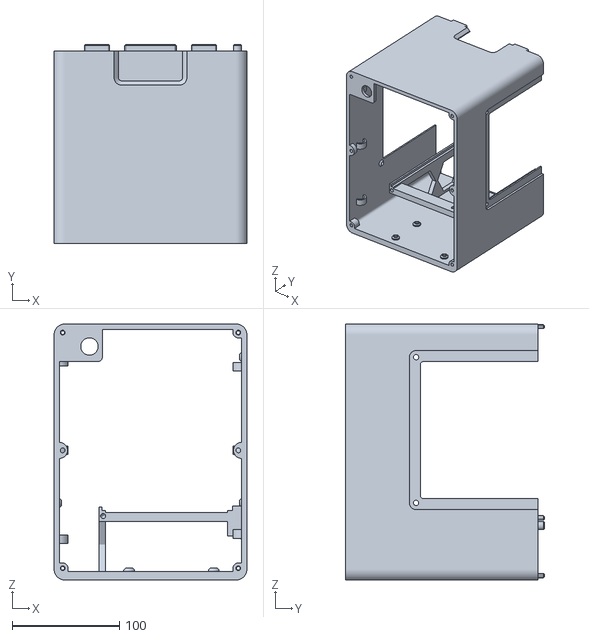
[picture p72: CAD file, 2026-08-19]
references/printables-1652979-quiet-case/Deepcool Edition - Digital Display/front-case.stl
180.0 x 186.0 x 239.0
