zloymalefic/bc250-case/references/printables-1652979-quiet-case/XL Version - Aftermath/case-back.stl

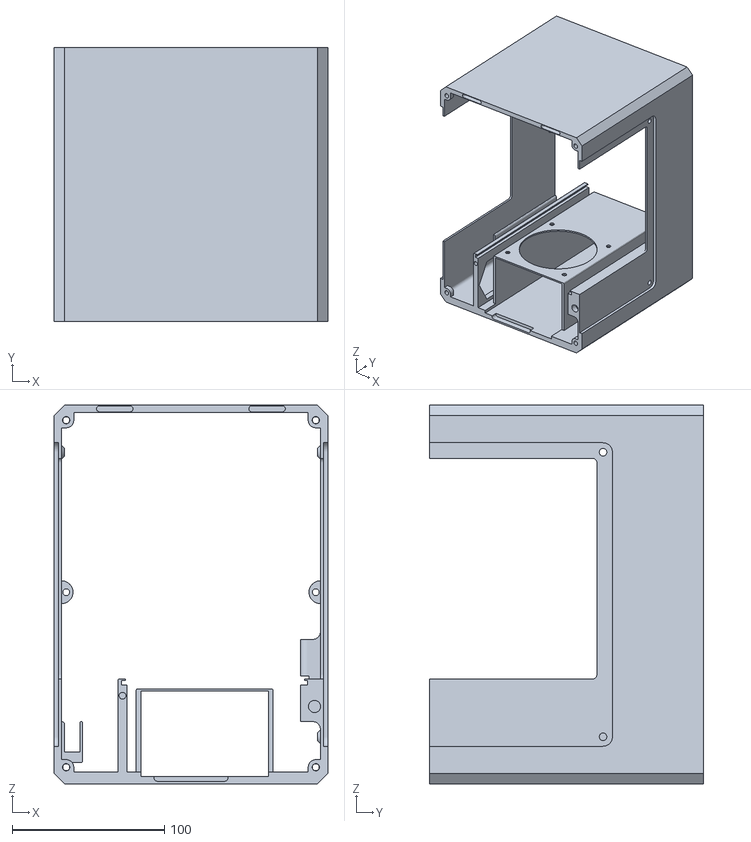
[picture p73: CAD file, 2026-08-19]
references/printables-1652979-quiet-case/XL Version - Aftermath/case-back.stl
180.0 x 180.0 x 249.0
