zloymalefic/bc250-case/references/printables-1793043-nexgen-pro-v2/AIO Mount/thumbnut-mount-tensioner-v2.3mf

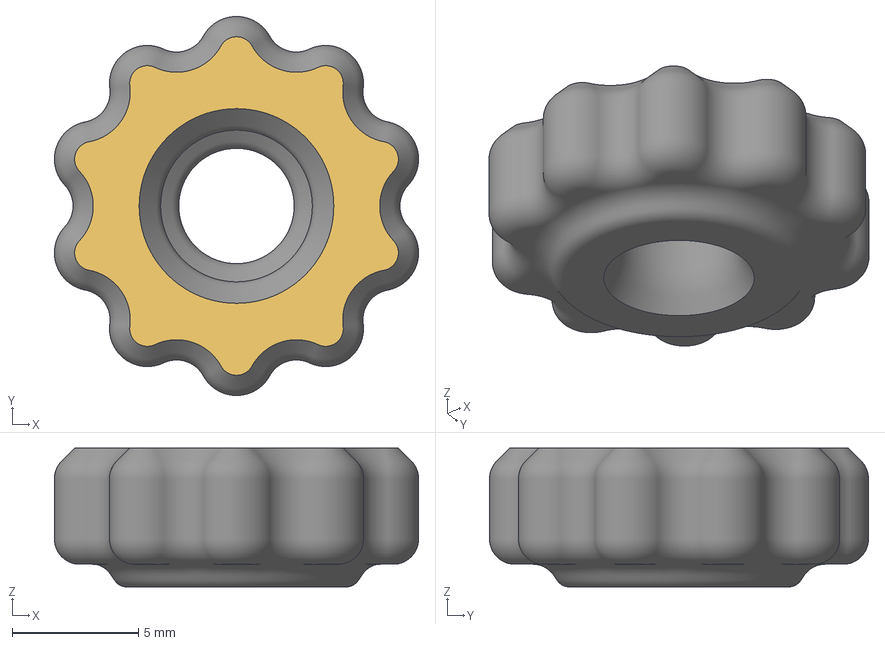
[picture p75: CAD file, 2026-08-19]
references/printables-1793043-nexgen-pro-v2/AIO Mount/thumbnut-mount-tensioner-v2.3mf
14.4 x 15.0 x 5.50 mm
