zloymalefic/bc250-case/references/printables-1793043-nexgen-pro-v2/Left Hand Hex Panel/pro-v2-access-panel-required.3mf

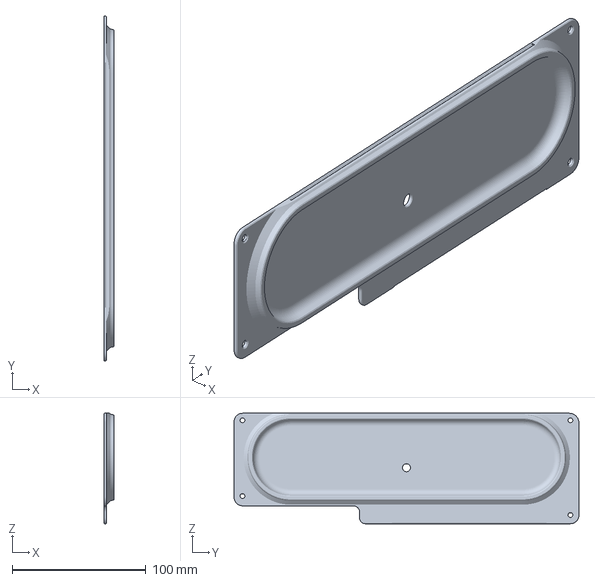
[picture p76: CAD file, 2026-08-19]
references/printables-1793043-nexgen-pro-v2/Left Hand Hex Panel/pro-v2-access-panel-required.3mf
7.80 x 257.6 x 82.5 mm
