zloymalefic/bc250-case/references/printables-1793043-nexgen-pro-v2/Power Supply Mounts/pro-v2-server-psu-mount-hp-dell-lenovo.3mf

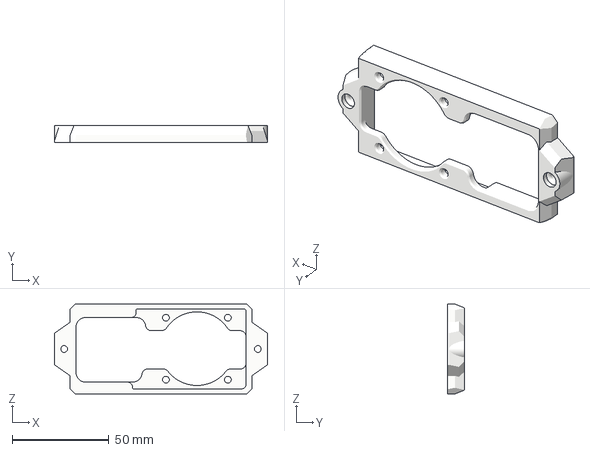
[picture p77: CAD file, 2026-08-19]
references/printables-1793043-nexgen-pro-v2/Power Supply Mounts/pro-v2-server-psu-mount-hp-dell-lenovo.3mf
110.0 x 9.00 x 46.3 mm
