zloymalefic/bc250-case/visualization/assets/front-core.stl

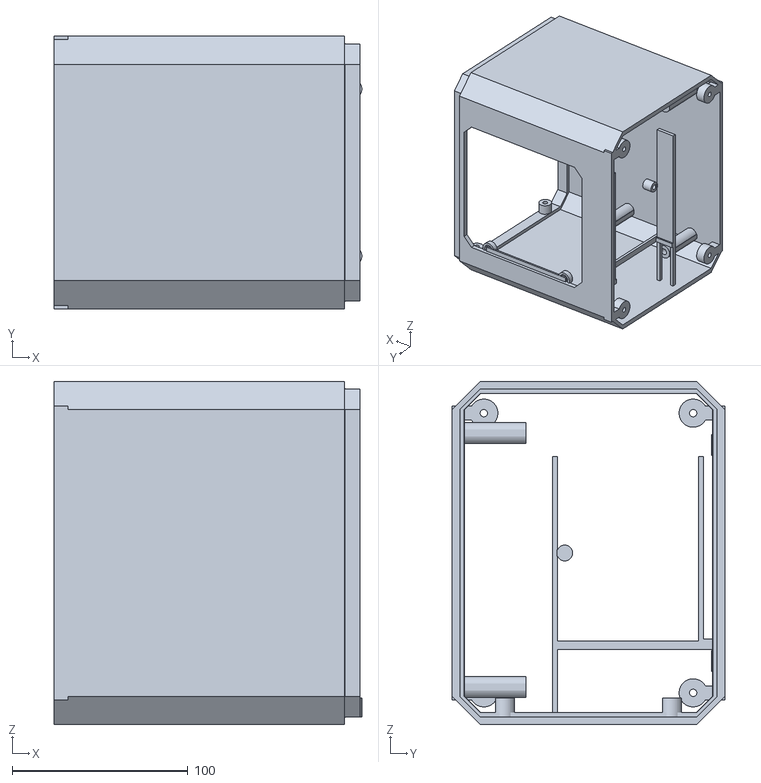
[picture p78: CAD file, 2026-08-20]
visualization/assets/front-core.stl
175.0 x 155.0 x 195.0
