zloymalefic/bc250-case/cad/exports/support-horizontal-v0.1.stl

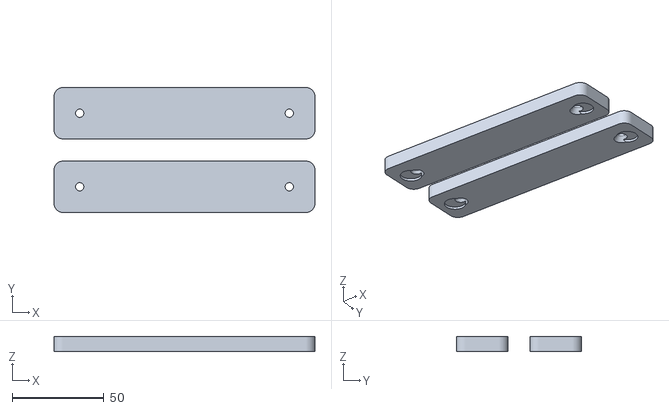
[picture p79: CAD file, 2026-08-20]
cad/exports/support-horizontal-v0.1.stl
142.0 x 68.0 x 8.00
