zloymalefic/bc250-case/references/printables-1649679-nexgen-redux/Face Plates V4.2.1 - Current Version/blank-button.step

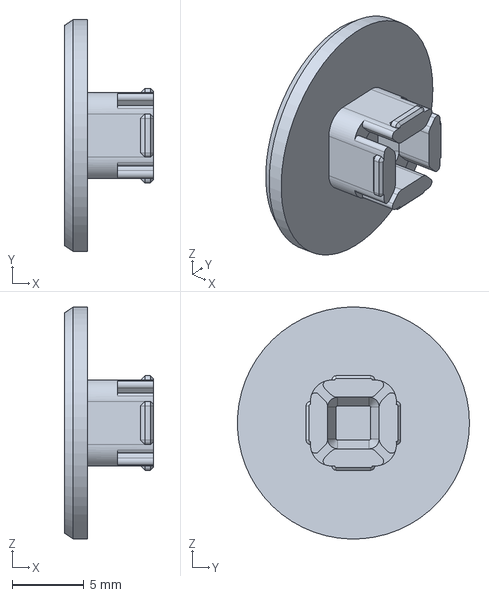
[picture p80: CAD file, 2026-08-20]
references/printables-1649679-nexgen-redux/Face Plates V4.2.1 - Current Version/blank-button.step
6.20 x 16.2 x 16.2 mm
