zloymalefic/bc250-case/references/printables-1649679-nexgen-redux/Face Plates V4.2/nexgen-button-to-convert-switch-to-momentary.3mf

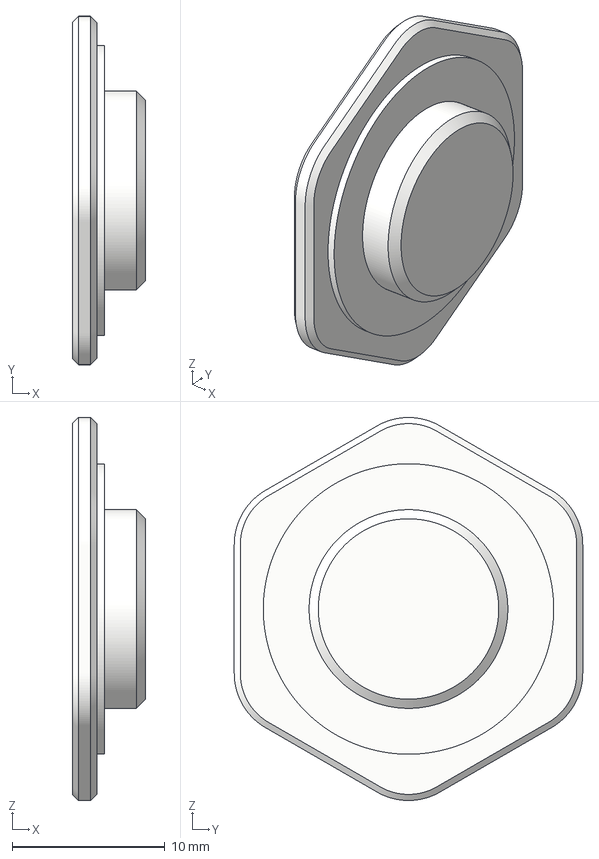
[picture p81: CAD file, 2026-08-20]
references/printables-1649679-nexgen-redux/Face Plates V4.2/nexgen-button-to-convert-switch-to-momentary.3mf
4.80 x 22.8 x 25.1 mm
Accent-1
Accent-2
NexGen Button Momentary
