zloymalefic/bc250-case/references/printables-1649679-nexgen-redux/Split Hex Covers for Odd Ball Prusa Beds (250x210)/prusa-priners-only-top-split-panel-b.3mf

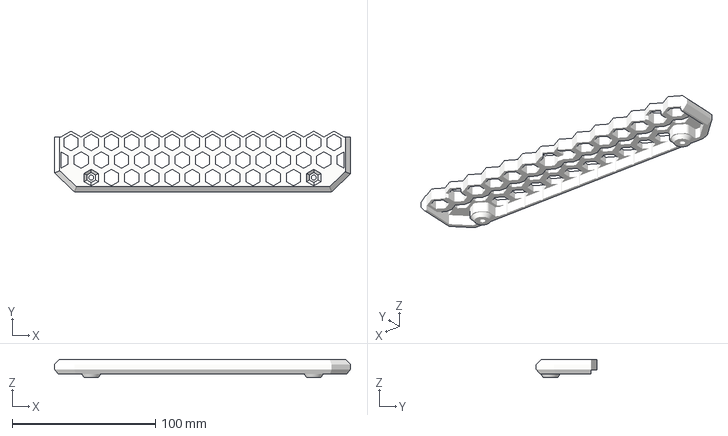
[picture p83: CAD file, 2026-08-20]
references/printables-1649679-nexgen-redux/Split Hex Covers for Odd Ball Prusa Beds (250x210)/prusa-priners-only-top-split-panel-b.3mf
206.8 x 42.4 x 12.9 mm
