zloymalefic/bc250-case/references/printables-1652979-quiet-case/Deepcool Edition - Digital Display/front-panel.stl

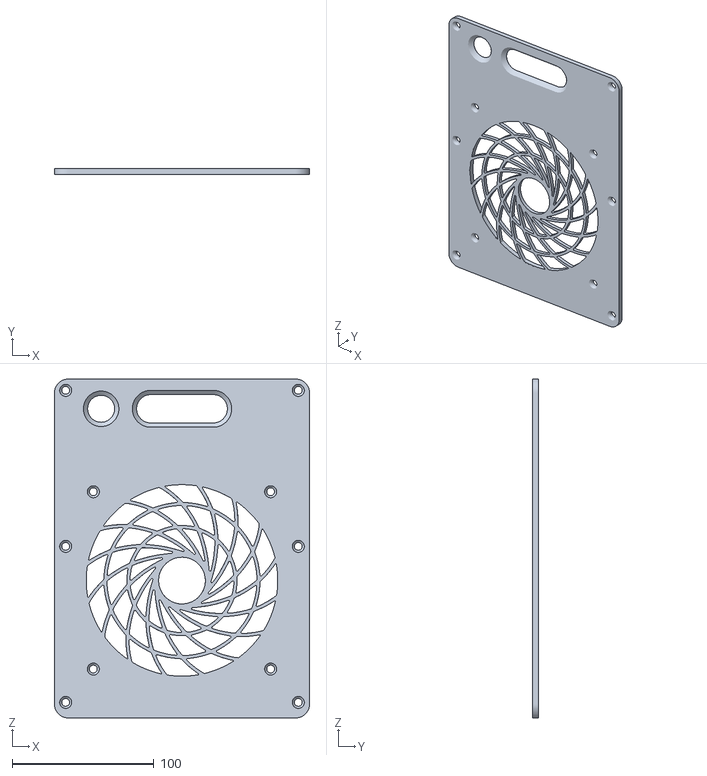
[picture p84: CAD file, 2026-08-19]
references/printables-1652979-quiet-case/Deepcool Edition - Digital Display/front-panel.stl
180.0 x 4.01 x 239.0
