zloymalefic/bc250-case/references/printables-1652979-quiet-case/XL Version - Aftermath/stand-model-2.stl

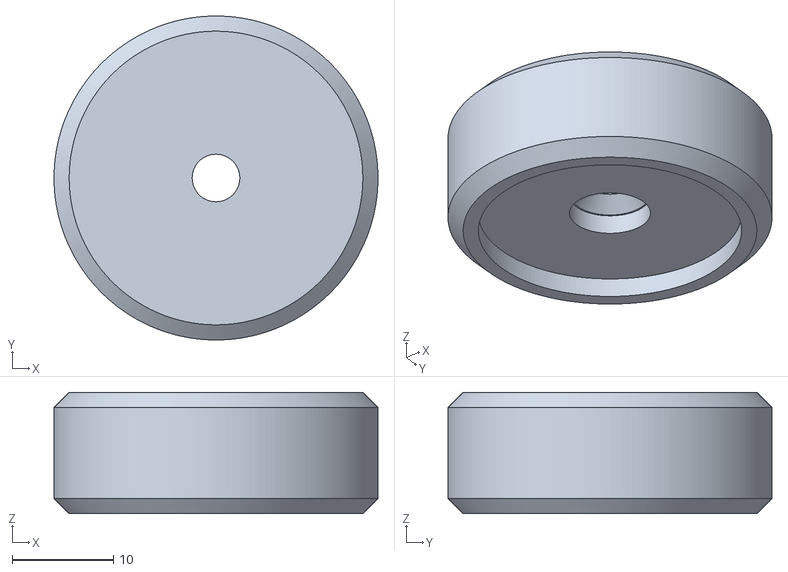
[picture p85: CAD file, 2026-08-19]
references/printables-1652979-quiet-case/XL Version - Aftermath/stand-model-2.stl
32.0 x 32.0 x 12.0
