zloymalefic/bc250-case/references/printables-1793043-nexgen-pro-v2/AIO Mount/spring-seat-v2.3mf

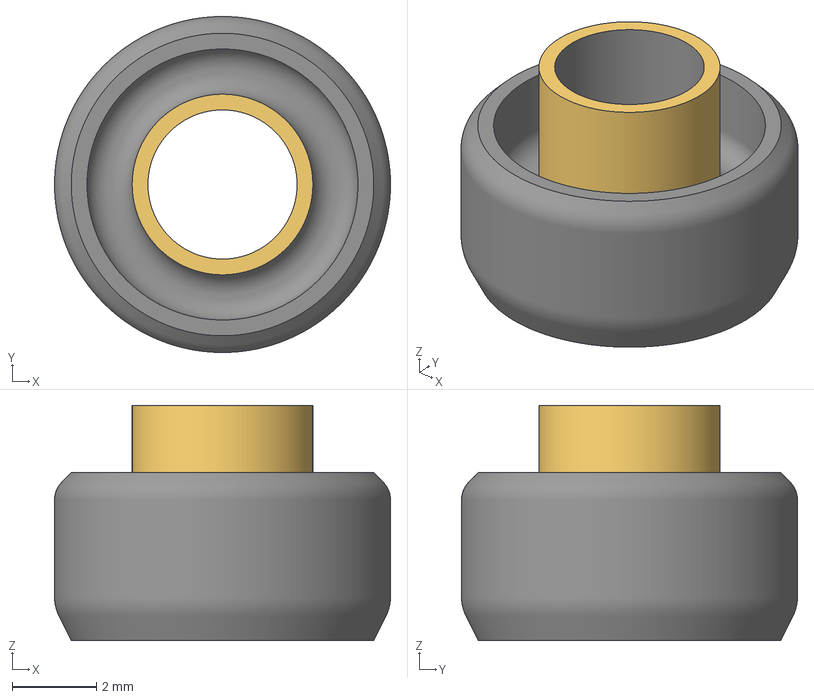
[picture p86: CAD file, 2026-08-19]
references/printables-1793043-nexgen-pro-v2/AIO Mount/spring-seat-v2.3mf
8.00 x 8.00 x 5.60 mm
