zloymalefic/bc250-case/references/printables-1793043-nexgen-pro-v2/Latest Face Plate Design - (Version 2.1)/faceplate-option-2.3mf

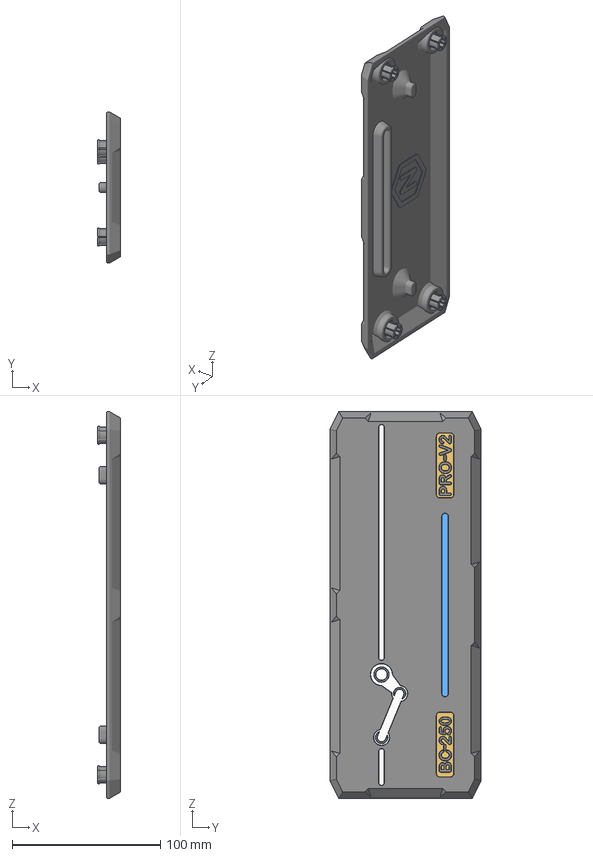
[picture p87: CAD file, 2026-08-19]
references/printables-1793043-nexgen-pro-v2/Latest Face Plate Design - (Version 2.1)/faceplate-option-2.3mf
15.7 x 102.0 x 260.9 mm
Accents (1)
Accents
BC-250 Logo (1)
BC-250 Logo (2)
BC-250 Logo (3)
BC-250 Logo
Faceplate
LED Strip
Pro Logo (1)
Pro Logo (2)
Pro Logo (3)
Pro Logo
Steam Logo (1)
Steam Logo
