zloymalefic/bc250-case/references/printables-1649679-nexgen-redux/Face Plates V4.2.1 - Current Version/steam-face-plate-button.3mf

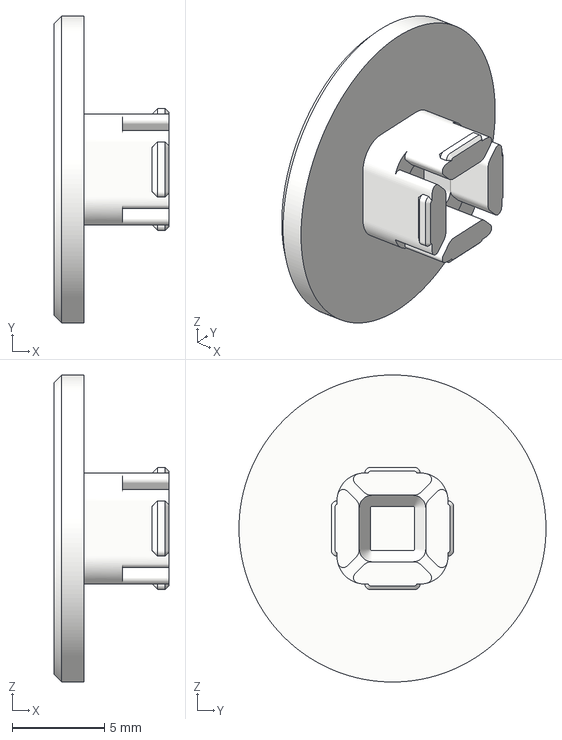
[picture p88: CAD file, 2026-08-20]
references/printables-1649679-nexgen-redux/Face Plates V4.2.1 - Current Version/steam-face-plate-button.3mf
6.20 x 16.6 x 16.6 mm
Black
White
