zloymalefic/bc250-case/references/printables-1652979-quiet-case/Deepcool Edition - Digital Display/back-panel.stl

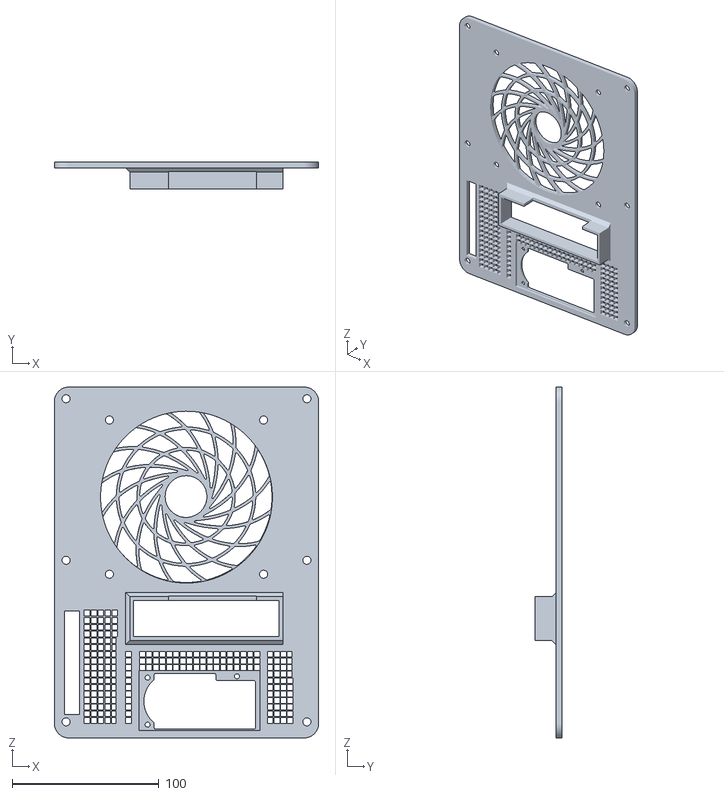
[picture p90: CAD file, 2026-08-19]
references/printables-1652979-quiet-case/Deepcool Edition - Digital Display/back-panel.stl
180.0 x 18.5 x 239.0
