zloymalefic/bc250-case/references/printables-1652979-quiet-case/XL Version - Aftermath/case-front.stl

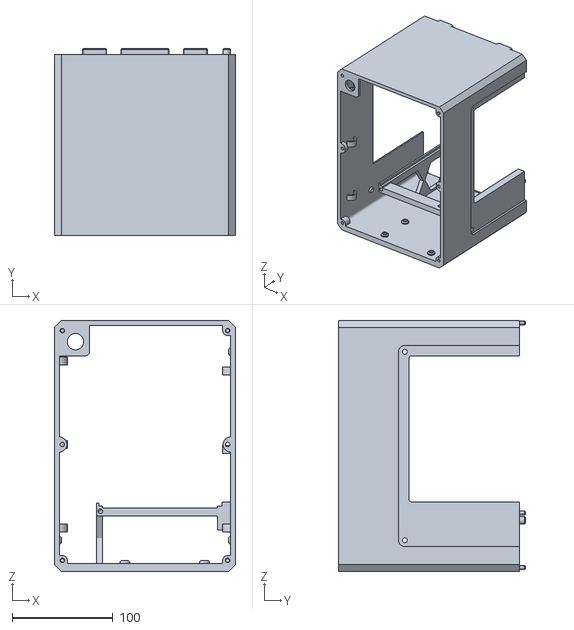
[picture p91: CAD file, 2026-08-19]
references/printables-1652979-quiet-case/XL Version - Aftermath/case-front.stl
180.0 x 186.0 x 249.0
