zloymalefic/bc250-case/references/printables-1737913-nyacom-flex/body-front_v24.stl

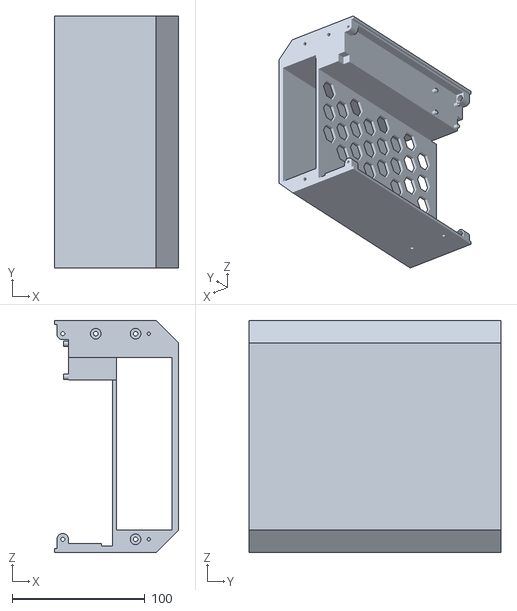
[picture p92: CAD file, 2026-08-19]
references/printables-1737913-nyacom-flex/body-front_v24.stl
93.8 x 190.0 x 175.0
