zloymalefic/bc250-case/references/printables-1793043-nexgen-pro-v2/AIO Mount/thumbnut-back-plate-retainer-v2.3mf

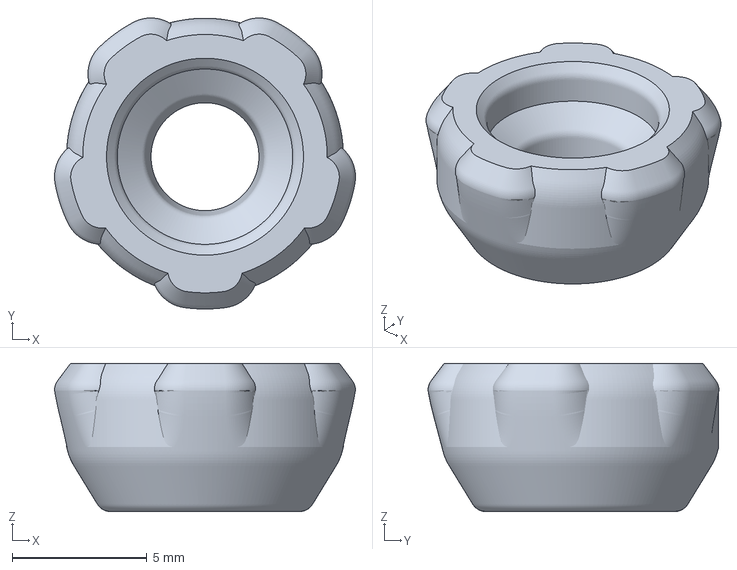
[picture p93: CAD file, 2026-08-19]
references/printables-1793043-nexgen-pro-v2/AIO Mount/thumbnut-back-plate-retainer-v2.3mf
11.2 x 10.8 x 5.50 mm
