zloymalefic/bc250-case/visualization/assets/front-button-mount.stl

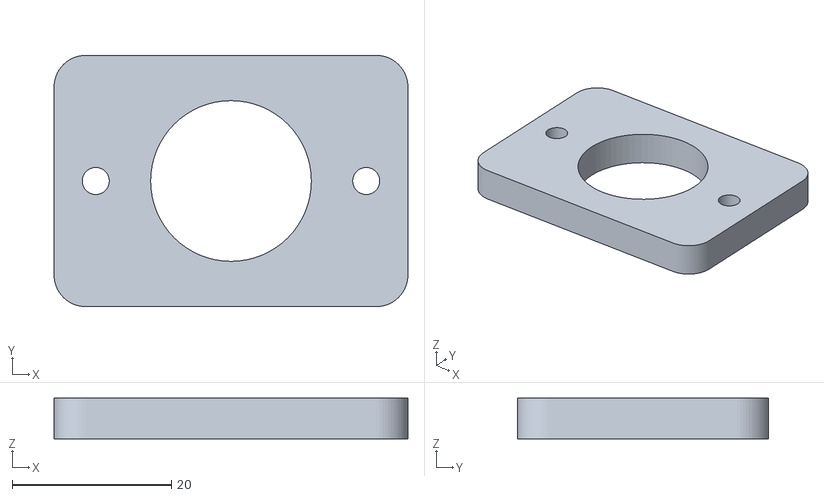
[picture p94: CAD file, 2026-08-20]
visualization/assets/front-button-mount.stl
44.5 x 31.6 x 5.10
