zloymalefic/bc250-case/references/printables-1649679-nexgen-redux/Case V4.2 - Current Version/lop-mounting-plate.3mf

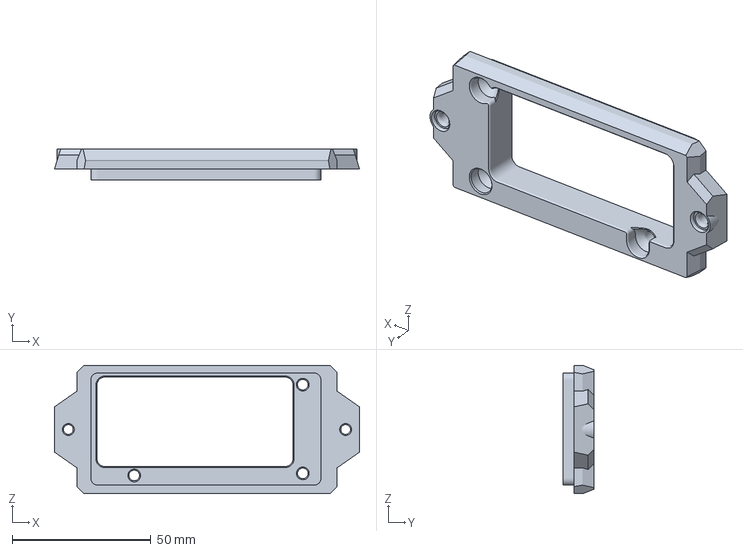
[picture p95: CAD file, 2026-08-20]
references/printables-1649679-nexgen-redux/Case V4.2 - Current Version/lop-mounting-plate.3mf
110.0 x 11.3 x 46.3 mm
