zloymalefic/bc250-case/references/printables-1652979-quiet-case/XL Version - Aftermath/panel-side.stl

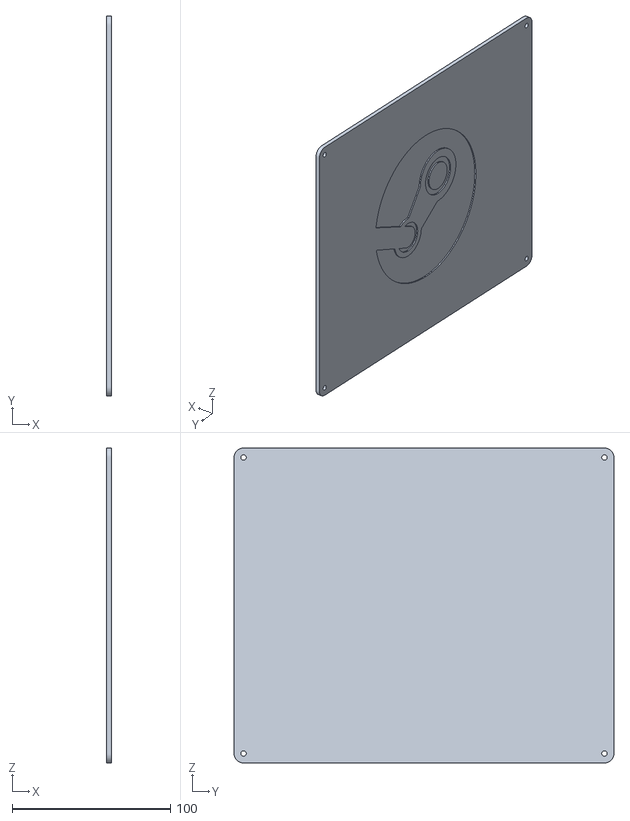
[picture p98: CAD file, 2026-08-19]
references/printables-1652979-quiet-case/XL Version - Aftermath/panel-side.stl
3.00 x 240.0 x 199.0
