zloymalefic/bc250-case/references/printables-1737913-nyacom-flex/body-rear-flex_v24_alpha.stl

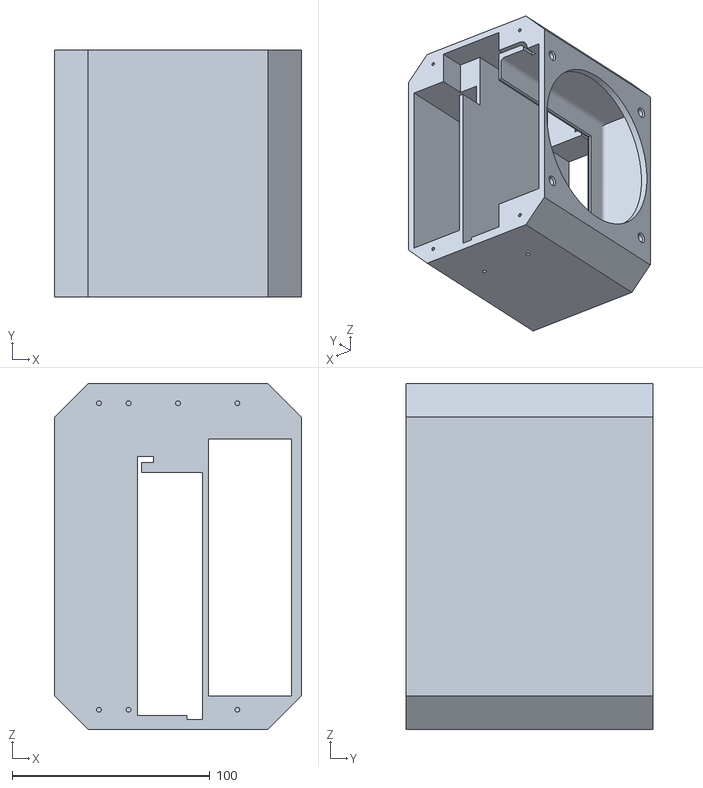
[picture p99: CAD file, 2026-08-19]
references/printables-1737913-nyacom-flex/body-rear-flex_v24_alpha.stl
125.0 x 125.0 x 175.0
