zloymalefic/bc250-case/visualization/assets/front-panel.stl

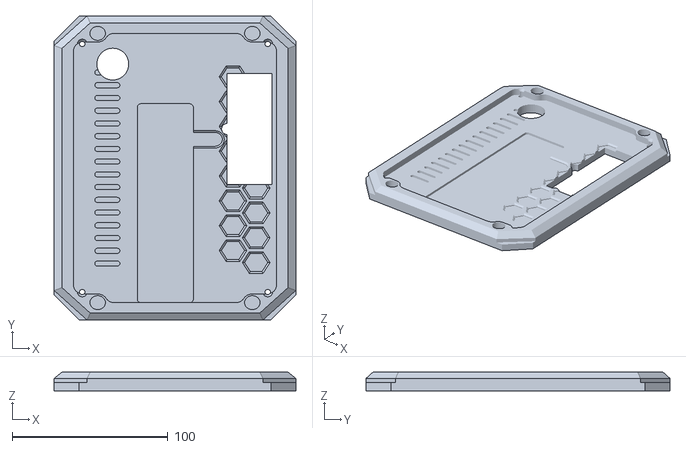
[picture p100: CAD file, 2026-08-20]
visualization/assets/front-panel.stl
155.0 x 195.0 x 12.0
