zloymalefic/bc250-case/references/printables-1649679-nexgen-redux/Case V4.2 - Current Version/server-psu-mount.3mf

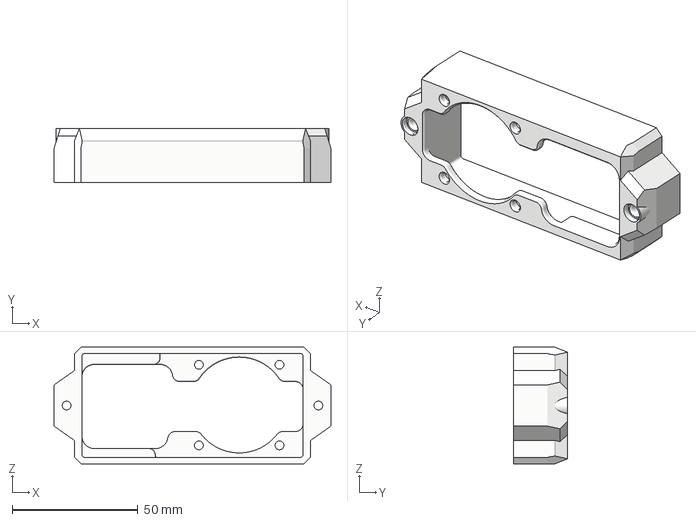
[picture p101: CAD file, 2026-08-20]
references/printables-1649679-nexgen-redux/Case V4.2 - Current Version/server-psu-mount.3mf
110.0 x 21.5 x 46.3 mm
