zloymalefic/bc250-case/references/printables-1737913-nyacom-flex/body-rear-panel-with-vents.stl

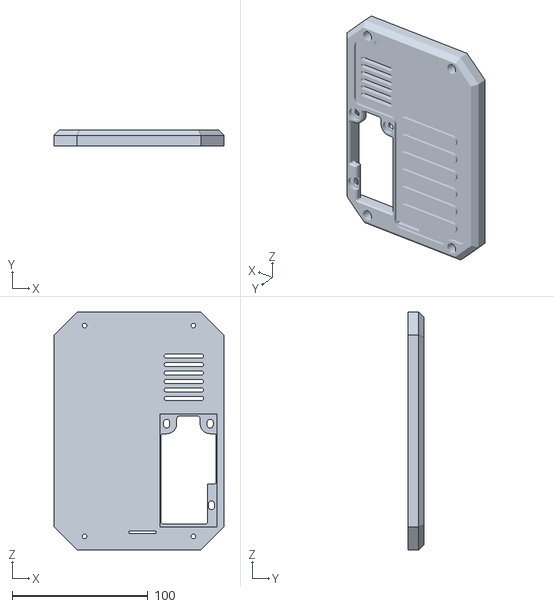
[picture p103: CAD file, 2026-08-19]
references/printables-1737913-nyacom-flex/body-rear-panel-with-vents.stl
125.0 x 12.0 x 175.0
