zloymalefic/bc250-case/visualization/assets/usb-cover.stl

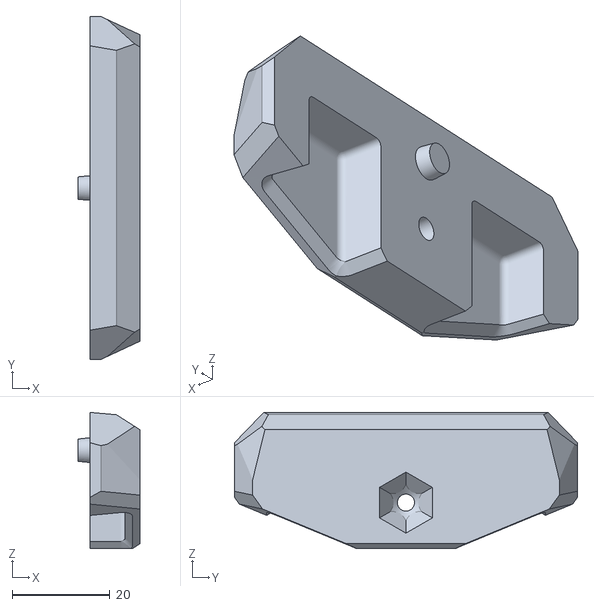
[picture p104: CAD file, 2026-08-20]
visualization/assets/usb-cover.stl
12.7 x 70.4 x 27.9
