zloymalefic/bc250-case/references/printables-1737913-nyacom-flex/body-front-panel-ssio.stl

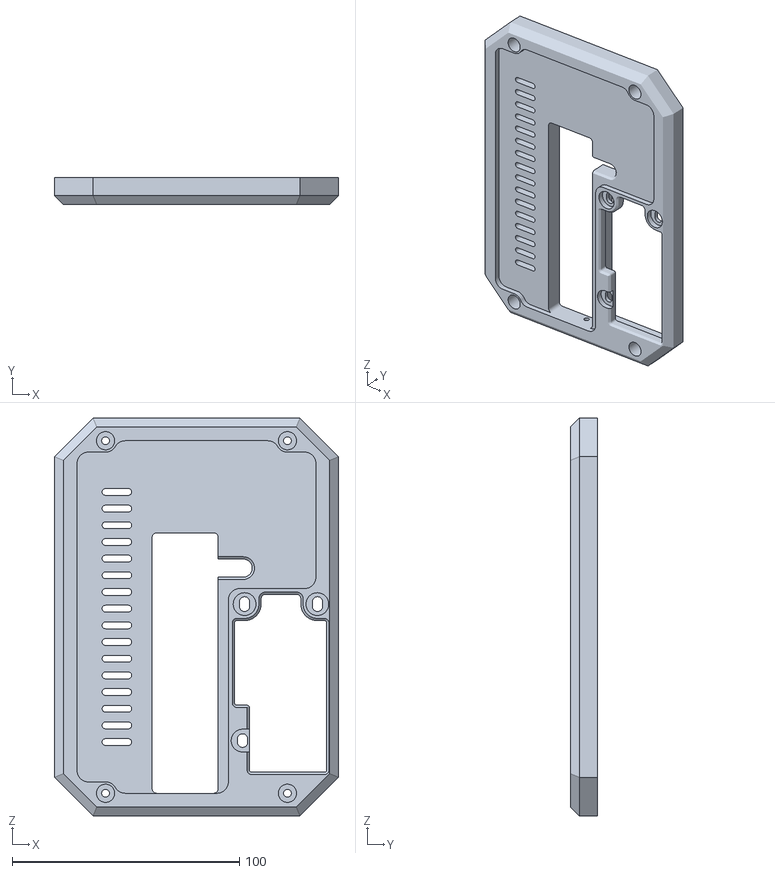
[picture p108: CAD file, 2026-08-19]
references/printables-1737913-nyacom-flex/body-front-panel-ssio.stl
125.0 x 12.0 x 175.0
