zloymalefic/bc250-case/visualization/assets/front-usb-cassette.stl

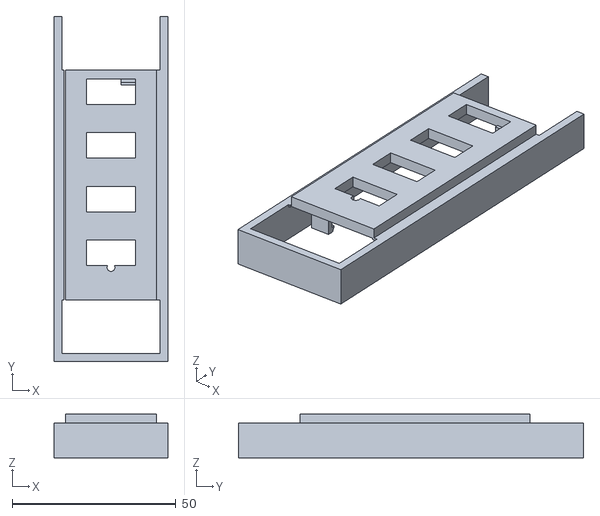
[picture p109: CAD file, 2026-08-20]
visualization/assets/front-usb-cassette.stl
34.8 x 105.4 x 13.4
