zloymalefic/bc250-case/references/printables-1649679-nexgen-redux/Face Plates V4.2.1 - Current Version/blank-faceplate.step

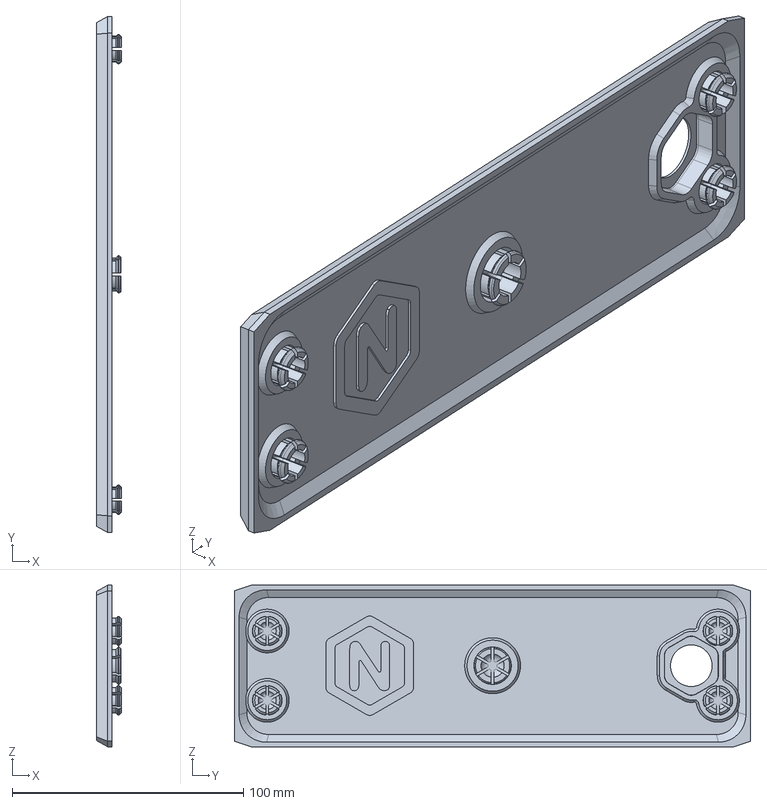
[picture p110: CAD file, 2026-08-20]
references/printables-1649679-nexgen-redux/Face Plates V4.2.1 - Current Version/blank-faceplate.step
10.8 x 223.2 x 69.9 mm
