zloymalefic/bc250-case/references/printables-1649679-nexgen-redux/Face Plates V4.2/simple-accent-redux-faceplate.3mf

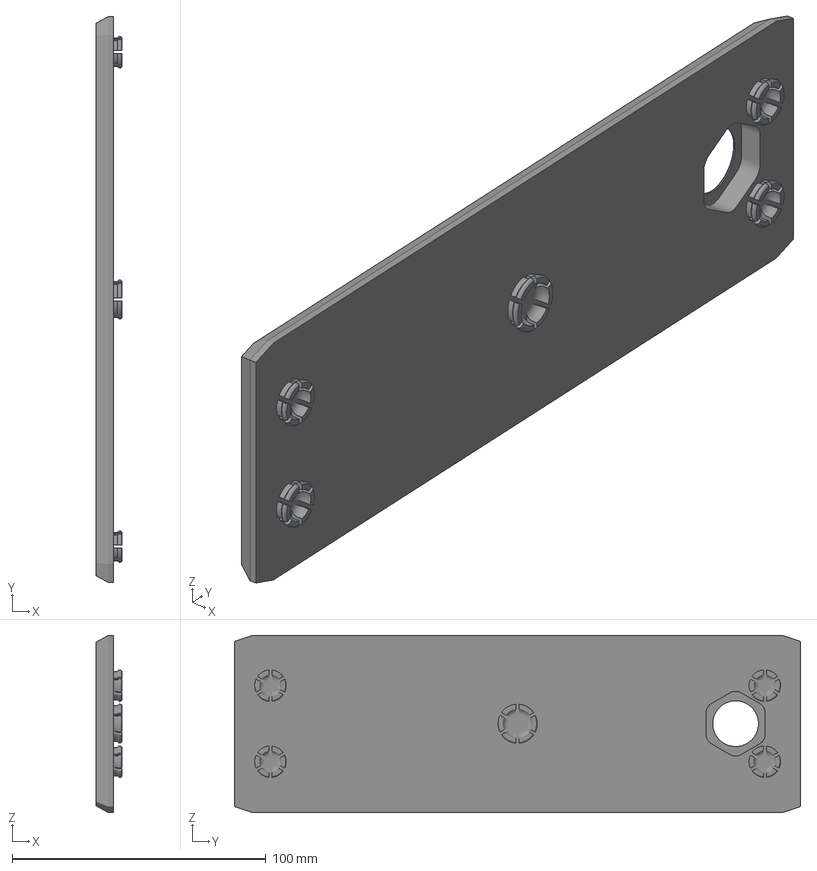
[picture p111: CAD file, 2026-08-20]
references/printables-1649679-nexgen-redux/Face Plates V4.2/simple-accent-redux-faceplate.3mf
10.2 x 223.2 x 69.9 mm
Accent-1
Accent-2
Faceplate
