zloymalefic/bc250-case/visualization/assets/rear-cover-horizontal.stl

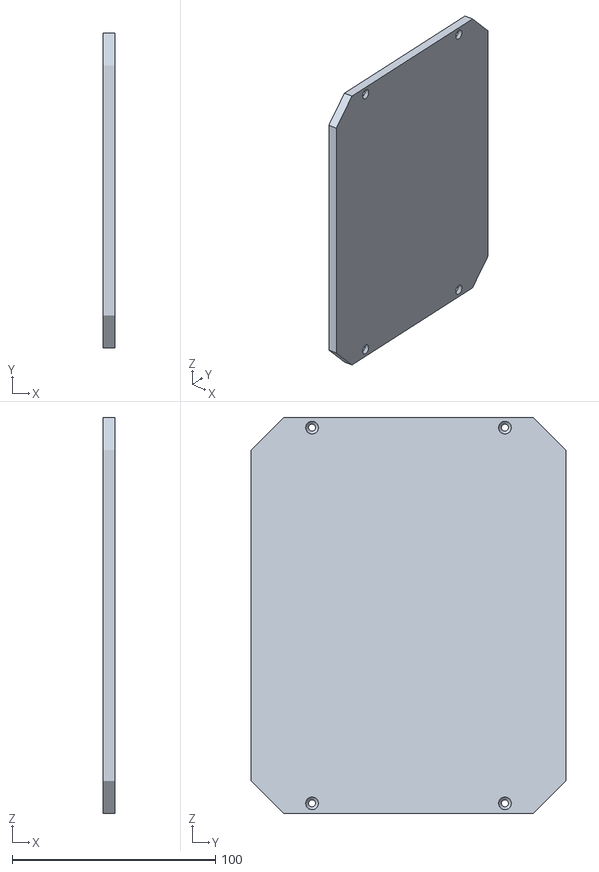
[picture p112: CAD file, 2026-08-20]
visualization/assets/rear-cover-horizontal.stl
6.00 x 155.0 x 195.0
