zloymalefic/bc250-case/references/printables-1649679-nexgen-redux/Case V4.2 - Current Version/psu-mounting-brackets.step

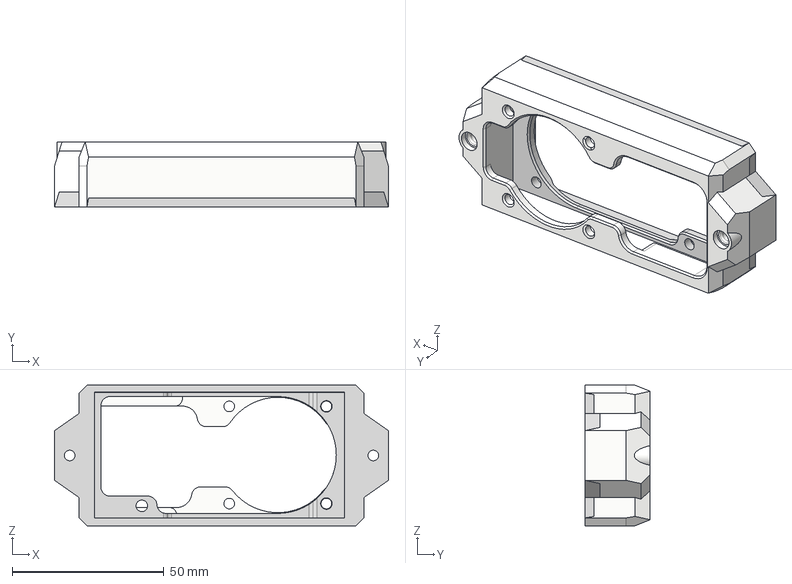
[picture p113: CAD file, 2026-08-20]
references/printables-1649679-nexgen-redux/Case V4.2 - Current Version/psu-mounting-brackets.step
110.0 x 21.5 x 46.3 mm
