zloymalefic/bc250-case/references/printables-1649679-nexgen-redux/Face Plates V4.2.1 - Current Version/display-button-body-fsp-mosfet-party.3mf

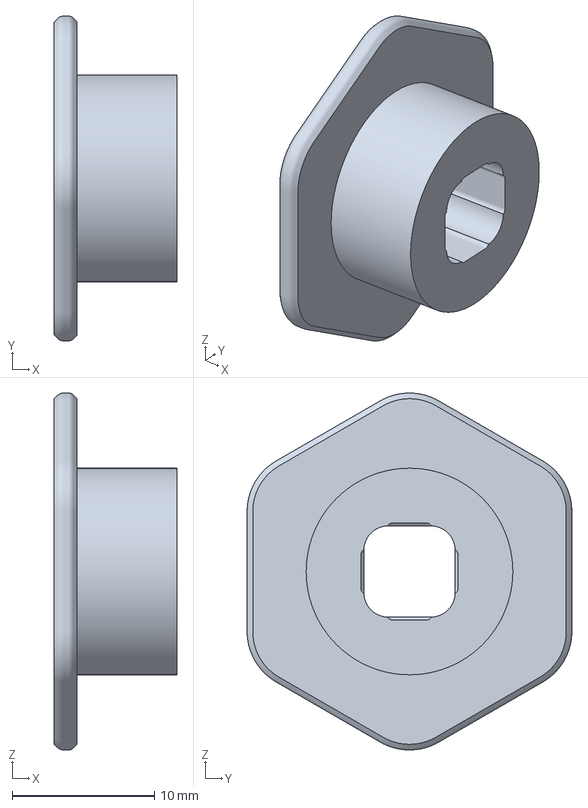
[picture p114: CAD file, 2026-08-20]
references/printables-1649679-nexgen-redux/Face Plates V4.2.1 - Current Version/display-button-body-fsp-mosfet-party.3mf
8.60 x 22.8 x 25.1 mm
