zloymalefic/bc250-case/references/printables-1649679-nexgen-redux/Face Plates V4.2/blank-button-to-convert-switch-to-momentary.3mf

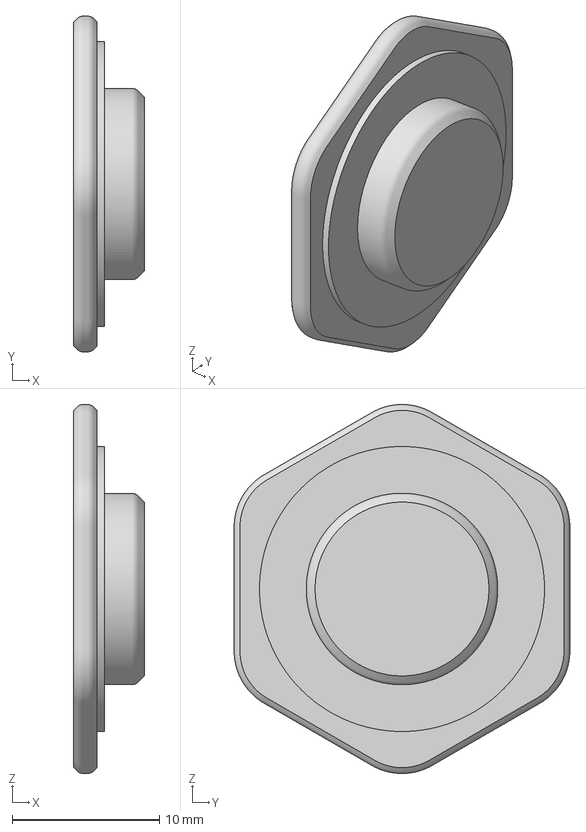
[picture p115: CAD file, 2026-08-20]
references/printables-1649679-nexgen-redux/Face Plates V4.2/blank-button-to-convert-switch-to-momentary.3mf
4.80 x 22.8 x 25.1 mm
