zloymalefic/bc250-case/visualization/assets/board-spine-front.stl

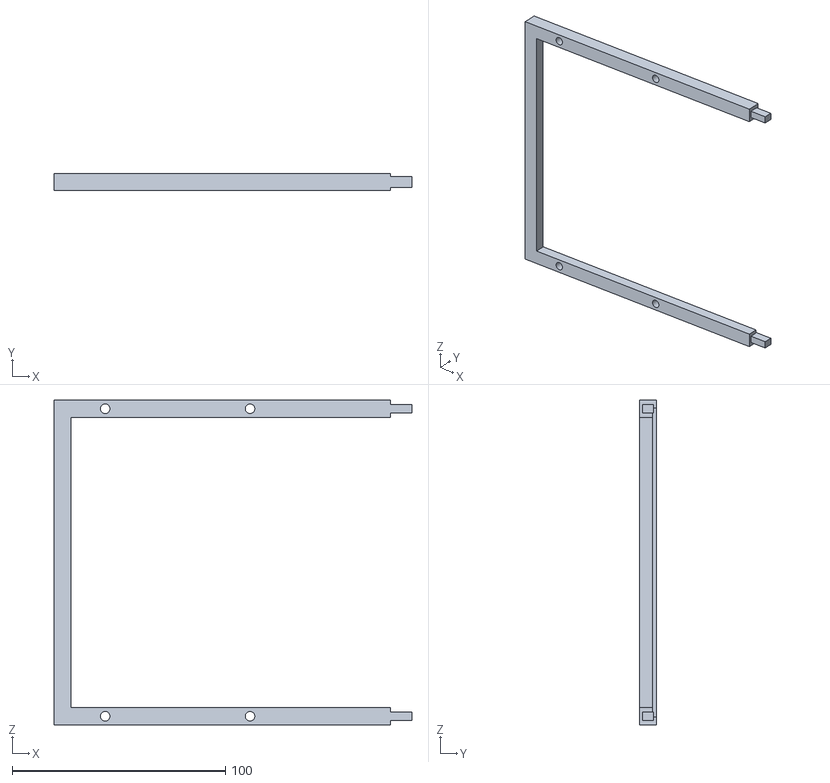
[picture p116: CAD file, 2026-08-20]
visualization/assets/board-spine-front.stl
168.0 x 8.00 x 152.3
