zloymalefic/bc250-case/references/printables-1649679-nexgen-redux/Face Plates V4.2.1 - Current Version/steam-logo-button.3mf

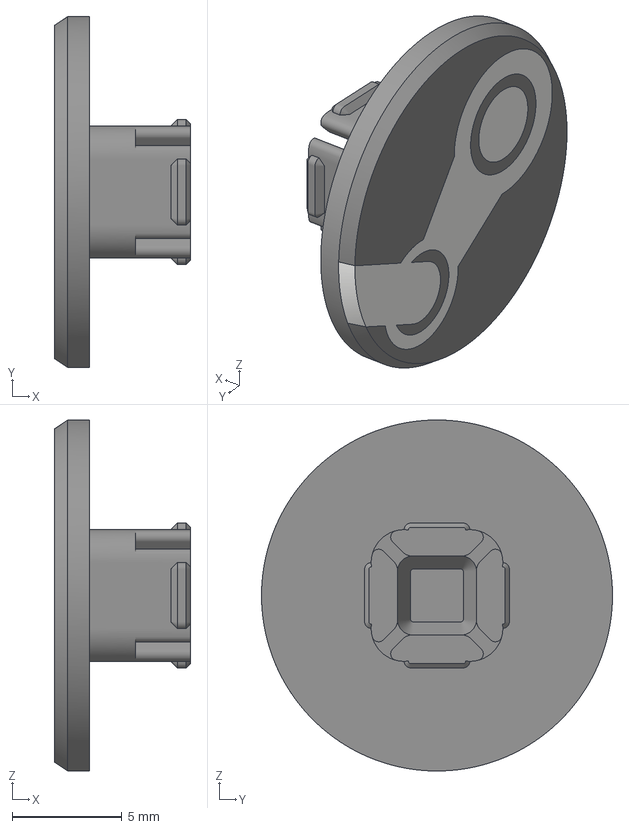
[picture p117: CAD file, 2026-08-19]
references/printables-1649679-nexgen-redux/Face Plates V4.2.1 - Current Version/steam-logo-button.3mf
6.20 x 16.0 x 16.0 mm
Black
White-1
White-2
