zloymalefic/bc250-case/references/printables-1649679-nexgen-redux/Face Plates V4.2/blank-button-for-fsp500-pcb.3mf

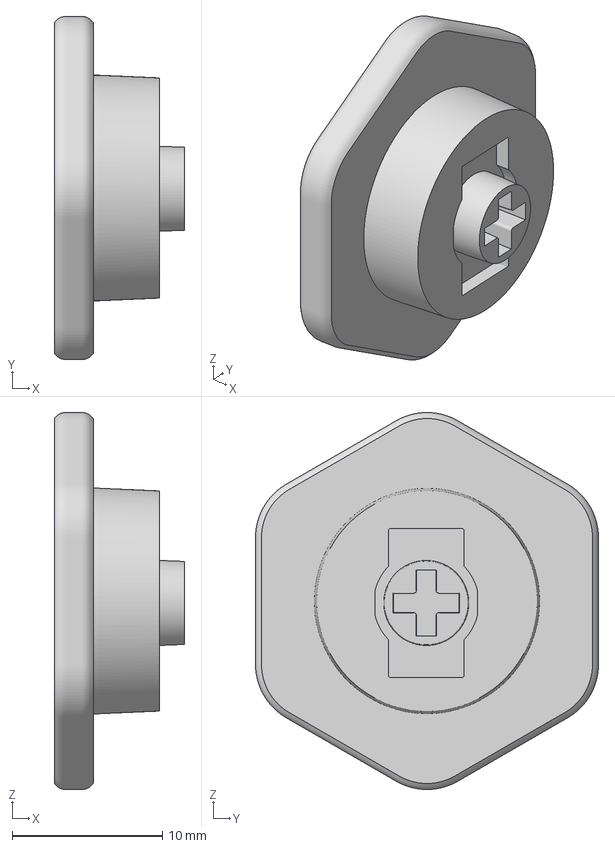
[picture p118: CAD file, 2026-08-20]
references/printables-1649679-nexgen-redux/Face Plates V4.2/blank-button-for-fsp500-pcb.3mf
8.67 x 22.8 x 25.1 mm
