zloymalefic/bc250-case/references/printables-1737913-nyacom-flex/body-cover-with-120mm-fan-magnetic-v2.stl

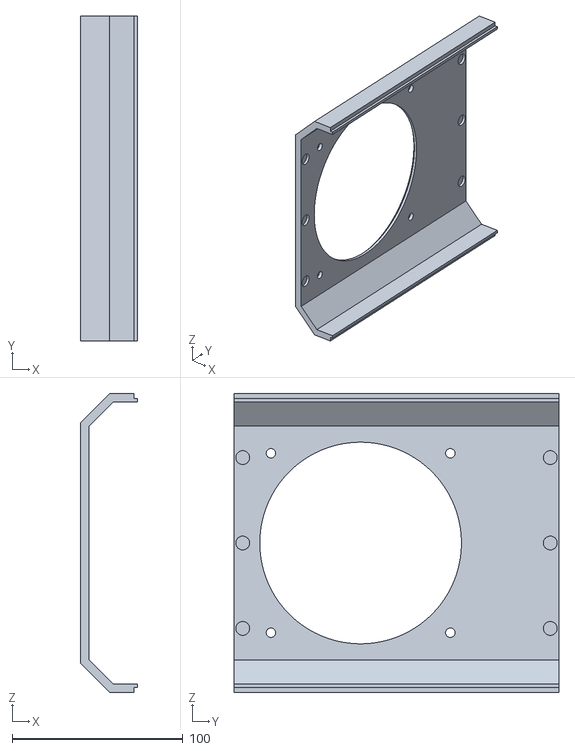
[picture p119: CAD file, 2026-08-19]
references/printables-1737913-nyacom-flex/body-cover-with-120mm-fan-magnetic-v2.stl
33.2 x 190.0 x 175.0
