zloymalefic/bc250-case/visualization/assets/esp32-cassette.stl

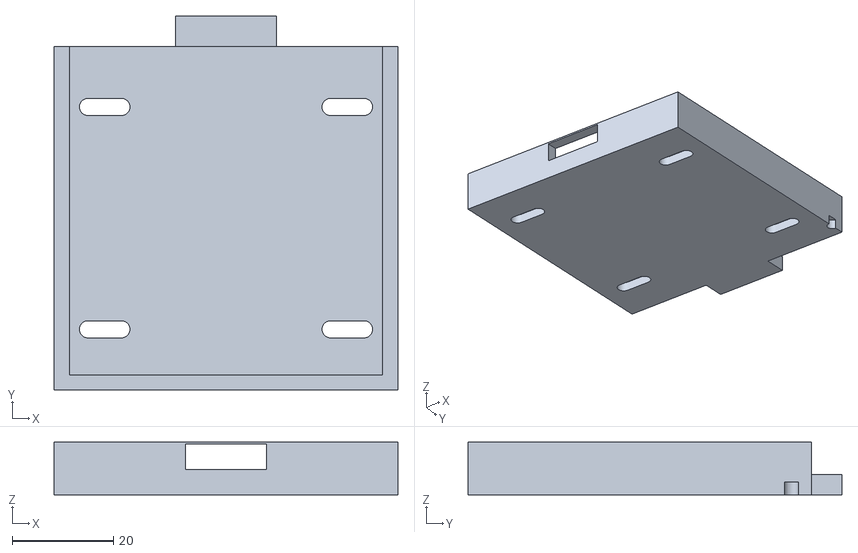
[picture p120: CAD file, 2026-08-20]
visualization/assets/esp32-cassette.stl
68.0 x 74.0 x 10.4
