zloymalefic/bc250-case/references/printables-1649679-nexgen-redux/Face Plates V4.2/blank-redux-faceplate.3mf

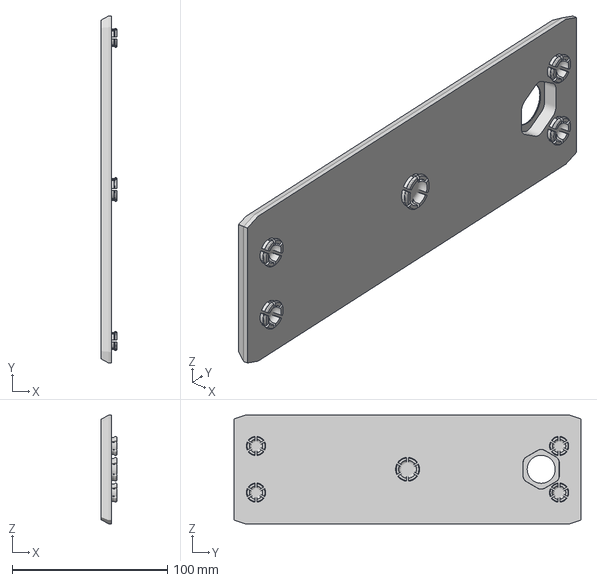
[picture p121: CAD file, 2026-08-20]
references/printables-1649679-nexgen-redux/Face Plates V4.2/blank-redux-faceplate.3mf
10.2 x 223.2 x 69.9 mm
