zloymalefic/bc250-case/references/printables-1737913-nyacom-flex/hdd-mounter-fan60.stl

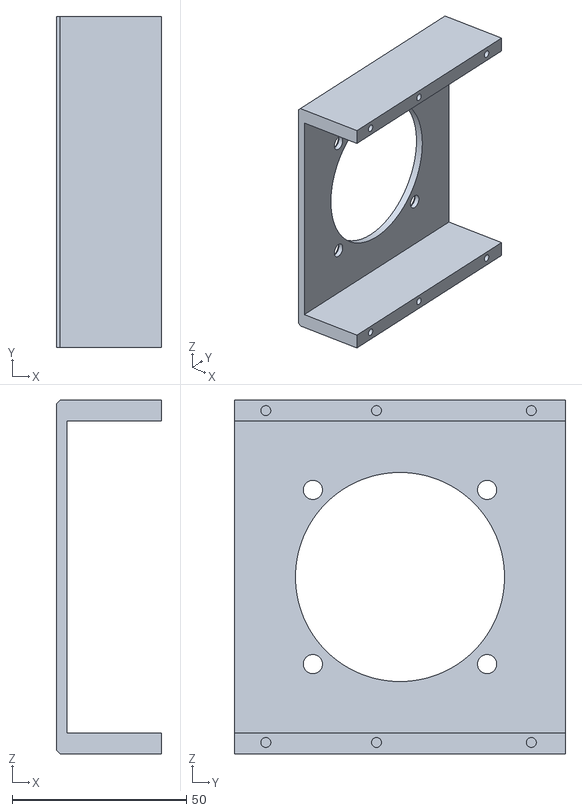
[picture p122: CAD file, 2026-08-19]
references/printables-1737913-nyacom-flex/hdd-mounter-fan60.stl
30.0 x 95.0 x 101.5
