zloymalefic/bc250-case/visualization/assets/ssd-cassette.stl

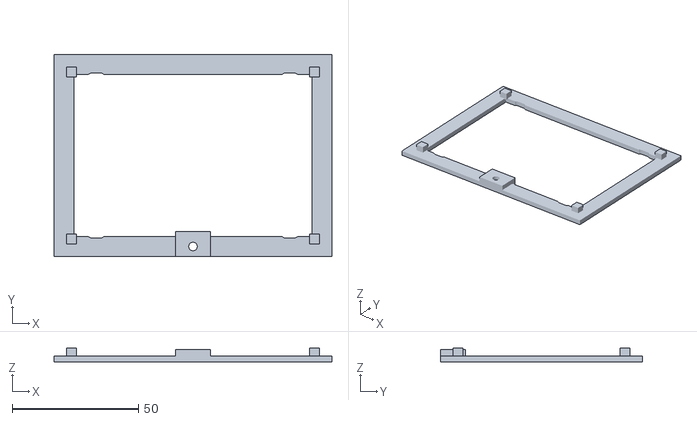
[picture p123: CAD file, 2026-08-20]
visualization/assets/ssd-cassette.stl
110.0 x 80.0 x 5.40
