zloymalefic/bc250-case/references/printables-1649679-nexgen-redux/Face Plates V4.2/display-panel-button-for-fsp500-pcb.3mf

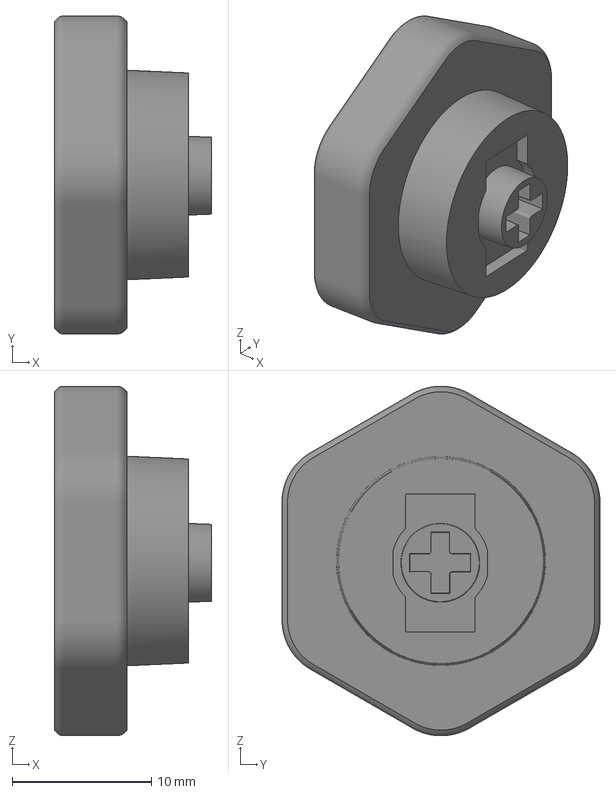
[picture p124: CAD file, 2026-08-20]
references/printables-1649679-nexgen-redux/Face Plates V4.2/display-panel-button-for-fsp500-pcb.3mf
11.3 x 22.8 x 25.1 mm
Accent-1
Accent-2
Accent-3
Button
