zloymalefic/bc250-case/references/printables-1737913-nyacom-flex/body-fan-edge-ring-steam.stl

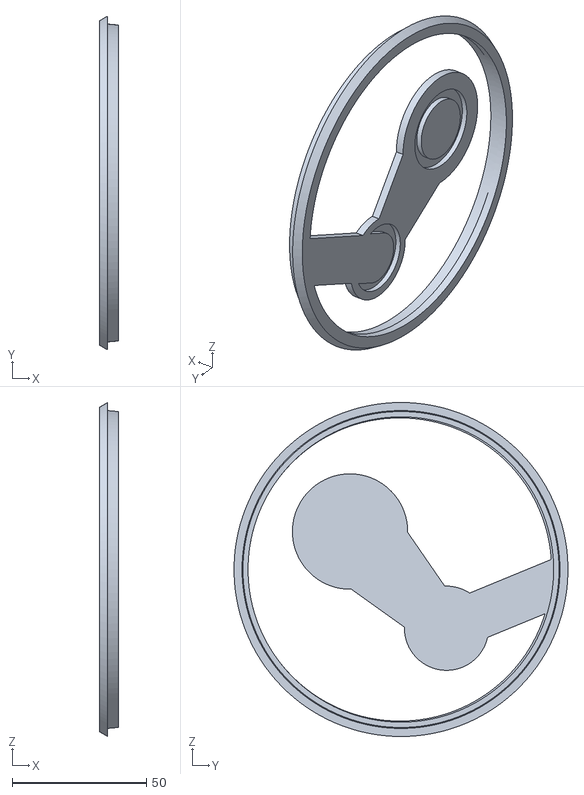
[picture p125: CAD file, 2026-08-19]
references/printables-1737913-nyacom-flex/body-fan-edge-ring-steam.stl
7.00 x 124.5 x 124.5
