zloymalefic/bc250-case/visualization/assets/button-logo-white.stl

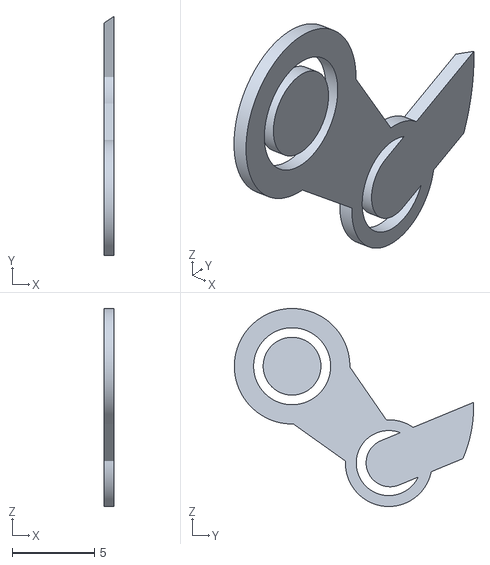
[picture p126: CAD file, 2026-08-20]
visualization/assets/button-logo-white.stl
0.6 x 14.5 x 12.0
