zloymalefic/bc250-case/cad/front-service-module-v0.1.scad

// Nyacom-style front service panel with replaceable NexGen button and USB hub cassette.
// All dimensions in millimetres. Baseline hub: Anker A7516 used by NexGen PRO V2.
include <lib/snap-interface.scad>
include <lib/interface-contracts.scad>

$fn = 48;

part = "assembly"; // panel | usb-cassette | assembly

// The source Nyacom panel is a complete 125 x 175 x 12 mm sculpted end cap.
// It is scaled only in its face plane to the project's 155 x 195 mm section;
// the original 12 mm depth, bevels and stepped surface remain intact.
panel = front_contract_size;
source_panel = [125, 175, 12];
button_opening = front_button_opening;
button_origin = front_button_origin;
usb_opening = front_usb_opening;
usb_origin = front_usb_origin;
panel_screw_points = front_contract_screws;
panel_screw_d = 3.4;
panel_screw_head_d = 6.4;
panel_screw_head_depth = 1.8;

// NexGen supplied cover: 70.35 x 27.93 x 12.65 mm raw mesh envelope.
// Anker publishes 103 x 30 x 10 mm for the short-cable A7516 body.
usb_face = front_usb_face;
anker_hub = [30, 103, 10]; // panel X, panel Y, inward Z
hub_clearance = 0.40;
usb_a_cut = [15.0, 7.8];
usb_port_pitch = 16.4;
usb_port_y0 = 10.575;

button_plate = [44.5, 31.6, 5.1];
light_pipe_d = 19.8;
button_mount_pitch = 34;
button_boss_d = 9;
button_boss_depth = 6;
button_insert_pilot_d = 4.2;

module chamfered_panel_2d(width, height, cut) {
    polygon([
        [cut, 0], [width - cut, 0], [width, cut],
        [width, height - cut], [width - cut, height],
        [cut, height], [0, height - cut], [0, cut]
    ]);
}

module nyacom_sculpted_panel() {
    scale([panel[0] / source_panel[0],
           panel[1] / source_panel[1], 1])
        multmatrix([
            [1, 0, 0, 62.5],
            [0, 0, 1, 87.5],
            // Source Y=-174 is the sculpted exterior and Y=-162 is the
            // internal mounting face. Map exterior to local Z=12.
            [0, -1, 0, -162],
            [0, 0, 0, 1]
        ])
            import("../references/printables-1737913-nyacom-flex/body-front-panel.stl");
}

module capsule(length, width, depth) {
    hull() {
        translate([-length / 2 + width / 2, 0, 0]) cylinder(h = depth, d = width);
        translate([ length / 2 - width / 2, 0, 0]) cylinder(h = depth, d = width);
    }
}

module rounded_rect_pocket(size, radius, depth) {
    hull()
        for (x = [radius, size[0] - radius],
             y = [radius, size[1] - radius])
            translate([x, y, 0]) cylinder(h = depth, r = radius);
}

module front_panel() {
    color([0.94, 0.72, 0.05]) union() {
        difference() {
            union() {
                nyacom_sculpted_panel();
                // Continuous inner datum ties the source panel's ornamental
                // ribs into one printable structural end cap after new cuts.
                // The 5.2 mm inner structural layer also absorbs the source
                // model's legacy snap posts/holes; none remain exposed or
                // printable as disconnected remnants in this bolted version.
                linear_extrude(height = 5.2)
                    chamfered_panel_2d(panel[0], panel[1], 16);
            }

            button_center = [button_origin[0] + button_opening[0] / 2,
                             button_origin[1] + button_opening[1] / 2];
            // Only the light-pipe/pusher passage reaches the exterior. The
            // complete NexGen mounting plate is fastened against the inside.
            translate([button_center[0], button_center[1], -0.1])
                cylinder(h = panel[2] + 0.2, d = light_pipe_d + 0.6);
            for (x = [button_center[0] - button_mount_pitch / 2,
                      button_center[0] + button_mount_pitch / 2])
                translate([x, button_center[1], -0.1])
                    cylinder(h = 6.2,
                             d = button_insert_pilot_d);

            // Replaceable vertical Anker cassette opening.
            translate([usb_origin[0], usb_origin[1], -0.1])
                cube([usb_opening[0], usb_opening[1], panel[2] + 0.2]);

            // Concealed finger release notches at the module edges.
            translate([usb_origin[0] - 0.1,
                       usb_origin[1] + usb_opening[1] / 2, -0.1])
                cylinder(h = panel[2] + 0.2, d = 7);

            // Four front-access M3 countersunk screws retain the complete
            // service panel, matching the user's required bolted interface.
            for (p = panel_screw_points) {
                translate([p[0], p[1], -0.1])
                    cylinder(h = panel[2] + 0.2, d = panel_screw_d);
                translate([p[0], p[1],
                           panel[2] - panel_screw_head_depth])
                    cylinder(h = panel_screw_head_depth + 0.1,
                             d1 = panel_screw_d, d2 = panel_screw_head_d);
            }
        }

    }

}

module usb_cassette() {
    color([0.13, 0.14, 0.16])
    difference() {
        union() {
            cube(usb_face);

            // Open cradle extends inward. The 103 mm hub overhangs the visible
            // 70.35 mm port cover equally at both ends.
            hub_y = (usb_face[1] - anker_hub[1]) / 2;
            hub_x = (usb_face[0] - anker_hub[0]) / 2;
            translate([hub_x - 2.4, hub_y, -anker_hub[2] - hub_clearance])
                cube([2.4, anker_hub[1], anker_hub[2] + hub_clearance + 0.2]);
            translate([hub_x + anker_hub[0], hub_y,
                       -anker_hub[2] - hub_clearance])
                cube([2.4, anker_hub[1], anker_hub[2] + hub_clearance + 0.2]);
            translate([hub_x - 2.4, hub_y - 2.4,
                       -anker_hub[2] - hub_clearance])
                cube([anker_hub[0] + 4.8, 2.4,
                      anker_hub[2] + hub_clearance + 0.2]);
            // Thin lips join the wider 30 mm cradle to the 27.93 mm face
            // outside the hub's occupied depth.
            translate([hub_x - 2.4, 0, -0.4])
                cube([3.0, usb_face[1], 0.6]);
            translate([usb_face[0] - 0.4, 0, -0.4])
                cube([hub_x + anker_hub[0] + 2.4 - usb_face[0] + 0.4,
                      usb_face[1], 0.6]);
        }

        // Four USB-A data ports of the Anker A7516.
        for (i = [0 : 3])
            translate([(usb_face[0] - usb_a_cut[0]) / 2,
                       usb_port_y0 + i * usb_port_pitch, -0.1])
                cube([usb_a_cut[0], usb_a_cut[1], usb_face[2] + 0.2]);

        // Small indicator aperture; optional and easy to blank.
        translate([usb_face[0] / 2, 10, -0.1]) cylinder(h = usb_face[2] + 0.2, d = 2.4);
    }

    // Two internal hooks retain the cassette in the standard front opening.
    translate([8, 2.2, 0]) scale([0.72, 0.72, 0.72]) snap_hook();
    translate([usb_face[0] - 8, usb_face[1] - 2.2, 0])
        rotate([0, 0, 180]) scale([0.72, 0.72, 0.72]) snap_hook();
}

module button_envelope() {
    // Envelope of the separate NexGen-derived mounting plate.
    color([0.12, 0.13, 0.15])
        cube([44.5, 31.6, 5.1]);
}

if (part == "panel") front_panel();
else if (part == "usb-cassette") usb_cassette();
else {
    front_panel();
    translate([button_origin[0] + 0.35, button_origin[1] + 0.35,
               panel[2] - button_plate[2]]) button_envelope();
    translate([usb_origin[0] + (usb_opening[0] - usb_face[0]) / 2,
               usb_origin[1] + (usb_opening[1] - usb_face[1]) / 2,
               panel[2]]) usb_cassette();
}

echo("part", part);
echo("front_panel_mm", panel);
echo("button_opening_mm", button_opening);
echo("usb_cassette_face_mm", usb_face);
echo("baseline_hub", "Anker A7516 4-port USB 3.0 hub");
echo("anker_hub_envelope_mm", anker_hub);
echo("button_fasteners", "2x M3 into rear bosses");
echo("front_panel_retention", "4x front-access M3 countersunk screws");
assert(panel[0] <= 250 && panel[1] <= 250, "Front panel exceeds 250 mm print-bed limit");
assert(usb_face[0] <= usb_opening[0] && usb_face[1] <= usb_opening[1],
       "USB cassette face no longer fits its front-panel opening");
assert(button_origin[0] >= 0 && button_origin[1] >= 0 &&
       button_origin[0] + button_opening[0] <= panel[0] &&
       button_origin[1] + button_opening[1] <= panel[1],
       "Button interface leaves the front panel");
assert(usb_origin[0] >= 0 && usb_origin[1] >= 0 &&
       usb_origin[0] + usb_opening[0] <= panel[0] &&
       usb_origin[1] + usb_opening[1] <= panel[1],
       "USB interface leaves the front panel");
